druzvv-hash/r1-s3-logger/NOTES.md

# Current memory entry point

## 2026-09-28 — R3 PowerBox mechanical/interconnect baseline

FINAL PRE-ROUTING / NOT ROUTED: PowerBox now has six 3.2 mm NPTH M3 holes
with 8 mm four-layer keepouts, optional DNP J12 primary 2x8 and J13 isolated
2x5 generic 2.54 mm THT interfaces, and a dimensioned future-R3 envelope.
Exact coordinates/pinouts are in
`hardware/kicad/R3_PowerBox/docs/R3_BOARD_TO_BOARD_INTERFACE.md`. Use 15 mm
stack spacing: U3/U6 are 11.1 mm high, so 12 mm is conditional on upper-board
cutouts. Latest validation: 199 footprints including 6 PCB-only holes, 0
tracks/0 vias, ERC 0 errors/412 generator warnings, and zero clearance,
copper-edge, drill, annular, hole or courtyard DRC errors. Do not route until
the documented programming, thermal, enclosure, header/socket and bench gates
are closed.

## 2026-09-28 — R3 PowerBox KiCad workspace

FINAL PRE-ROUTING / NOT ROUTED: the canonical editable PowerBox source is
`hardware/kicad/R3_PowerBox/tools/generate_hierarchical.py`; generated KiCad,
PDF, BOM and reports are committed under the same project. The approved board
is 160 x 80 mm with 191 placed footprints, four copper layers, DIRTY -> PRIMARY
-> ISOLATION -> CLEAN zoning and a 3.0 mm all-layer functional-isolation
corridor. The architecture is 2S Li-ion -> BQ28Z610 -> BQ25798/STUSB4500 ->
switched `VSYS_MAIN` -> existing digital and isolated ADS/INA supplies.

Normal user power uses Q4 `DMP3007LSS-13`; BMS, PD and charging remain alive
when R3 is off. QON is a separate service/ship wake input. Raw BQ25798 STAT and
3.3 V `CHARGE_STATUS` are isolated by BAT54WS; J11 is the primary-only panel
interface. Latest checks: schematic PDF 11 pages, ERC 0 errors / 408 generated
library-grid warnings; critical PCB DRC geometry categories are zero; PCB has
0 tracks and 0 vias. Do not begin routing or order hardware until the blockers
in `docs/VERIFICATION.md` are closed: PD/BMS programming, Q2/Q3 and PPTC thermal
validation, TPS54302 at 6 V, RS3/INA light-load behavior, enclosure connector
clearance and approval of the functional-isolation rule.

## 2026-09-24 — shared session files and BLE resilience

R1 0.38 / CANBox 0.6.5 / R3 CC 0.2.1 deployed; STM32 CM7 LFN/UTC update
ST-LINK verified. R1/CANBox share UTC/group basenames and continue through BLE
loss; explicit offline STOP reconciles original session on reconnect. Hardware
R1/R3-controller tests PASS with no CAN frames; R1 finalized file integrity PASS.
Actual FatFs host test validates creation/modification fields and LFN. STM32
recording awaits ADS131 development (owner clarified), not yet ECO1 group member.
Earlier R1 HTTP outage cause unresolved; final short download PASS. No overnight
or load qualification. Viewer reader updated; running server needs restart.
[Contract, evidence, deployment and limits](../GLL%20CANBox/docs/SESSION_RESILIENCE_2026-09-24.md).

## 2026-09-23 — shared owner manual

Created the Ukrainian ecosystem manual with topology, entry points, workflows,
troubleshooting and evidence limits. Update it alongside user-visible changes.
Documentation only; no new build, firmware deployment or hardware acceptance.
[Manual](../lily-logger-r3/docs/manual/README.uk.md).

## 2026-09-23 — R3 primary CANBox integration verified

R3 now controls R1 and CANBox together and provides coarse UTC. R1 firmware
unchanged. Group START/STOP, saved R1 fallback and return to R3 passed;
25/25 post-return fresh/time samples, not precision acceptance. Canonical report:
../lily-logger-r3/docs/CANBOX_CONTROL.md. Existing averaging owner edits preserved.

## 2026-09-23 — CAN Live update deployed

Shared CAN assets deployed by OTA alongside existing0.37 owner changes.
88 tests/build PASS; real UI122722/0 live-ring losses, not hardware losslessness.
R1↔R3 unchanged; CANBox UTC invalid/service adapter missing.
See [deployment report](docs/CAN_LIVE_FIXES_2026-09-23.md).

## 2026-09-22 — shared CAN workspace

0.36-can-live-dev deployed via native COM9 to verified active app1 at 0x490000;
READY, generation 6. CAN tab and `/can`, preserving 0.35 OTA/timezone. Canonical
assets: ../GLL CANBox/workspace; contract: ../GLL CANBox/docs/CAN_WORKSPACE.md.
BLE service-only; browser traffic directly over CANBox USB/Wi-Fi. 88 tests/build
PASS; real R1-hosted CAN page + CANBox Wi-Fi 60 s, 12/12 concurrent BLE/time
samples PASS while idle. No loaded CAN/TX qualification. Fallback mode enabled.

## Memory checkpoint — 2026-09-21

### Current state and evidence
BENCH TESTED within the bounded 2026-09-21 report: 0.35-ota-dev deployed, browser OTA app0 -> app1; local display offset saved at +120, EEPROM generation 6. Do not assume live IP/COM/firmware remain unchanged.

### Canonical references
- [docs/R1_S3_PLAN.md](docs/R1_S3_PLAN.md)
- [docs/DEVICE_UI_AND_TASKS.md](docs/DEVICE_UI_AND_TASKS.md)
- [docs/FILE_FORMAT_V2.md](docs/FILE_FORMAT_V2.md)
- [docs/UART_DIAGNOSTICS.md](docs/UART_DIAGNOSTICS.md)
- [docs/RATE_BENCHMARK.md](docs/RATE_BENCHMARK.md)
- [docs/OTA.md](docs/OTA.md)
- [docs/R5_FEATURE_MIGRATION.md](docs/R5_FEATURE_MIGRATION.md)

### Negative knowledge / do not repeat
UART/CP210x: cleaning and cable changes did not prove a root cause; keep cause unresolved, see UART_DIAGNOSTICS. Native USB is a separate path; see CANBox stability report for core affinity evidence. Do not equate 300 Hz clean transport with analog accuracy, or a closed directory enumeration with a held SD transfer. Do not replace R5 tools with a reduced viewer and claim feature parity.

### Open work
Automatic timezone/DST and shared display-zone propagation remain IDEA; only R1 fixed local offset is deployed. Extend OTA fault/power-loss qualification, loaded UART isolation and noise/calibration qualification. Encoder remains a stub. Unified viewer work stays in lily-viewer.

### Dependencies
R3 time/control authority, CANBox fallback control, lily-viewer file readers; TTGO is an OTA/network reference only.

Shared time/control contract: [R3 ECOSYSTEM_CONTROL](../lily-logger-r3/docs/ECOSYSTEM_CONTROL.md). Read the sibling notes before changing it. A shared local timezone remains a requirement, not a completed cross-device feature.

---

# R1-S3 ideas and continuity

Read before changes and revisit at scope/milestone changes.

- [Engineering plan](docs/R1_S3_PLAN.md): acquisition, PSRAM buffering, SD block writer, UI and migration.
- [Migration history](docs/R1_MIGRATION.md): historical implementation and validation.
- [Work reports](WORK_REPORT.md): current dated work, tests, deployment and remaining tasks.
- [Ecosystem time](docs/ECOSYSTEM_TIME_SYNC.md): R3 Control Center is the preferred clock; R1 runs autonomously without it.
- R3's sibling `NOTES.md` contains ecosystem ideas and hardware evidence; review relevant entries rather than assuming all features are already implemented in R1.

## 2026-09-21 owner requirements

- Expose manual calendar entry and browser-clock fallback when valid R3 time is absent.
- Preserve authenticated Control Center priority; never move RTC during recording.
- Maintain separate project work reports; preserve existing ideas and notes.

## 2026-09-21 shared Wi-Fi

Use TTGO-style saved station networks and mDNS, keeping the R1 AP as a recovery
path. Credentials belong in private bootstrap/NVS, never notes or Git history.
Review WORK_REPORT.md for actual deployment and LAN validation.

## 2026-09-21 unified operator time

Owner requirement: every device must show the same synchronized local calendar
clock, including device screens, web panels, file lists, recording filenames and
viewer timelines. Operators must not have to mentally convert UTC. R3 Control
Center supplies the preferred clock AND the shared display timezone; standalone
manual/PC setup supplies the fallback. Do not choose each browser's timezone
independently. Keep canonical UTC/sample timing internally for cross-device
alignment and backward compatibility, and store the recording's timezone/offset
so historical display remains stable after travel or daylight-saving changes.
Existing UTC recordings must not be reinterpreted as local timestamps.
This requirement is recorded; cross-device timezone propagation is not yet
implemented. See WORK_REPORT.md.

R1-only implementation: 0.34-local-time-dev uses the existing saved offset for
UI/OLED/new filenames; PC sync refreshes that offset. Automatic DST and shared
R3 timezone distribution remain deferred. See docs/uk/TIME_SETTINGS.md.

R1 0.35 includes browser OTA (/update); see docs/OTA.md and the physical acceptance
in WORK_REPORT.md. Keep OTA idle-only and preserve storage/acquisition ownership.
