druzvv-hash/r1-s3-logger/docs/ECOSYSTEM_TIME_SYNC.md

# R3 / R1-S3 / CAN time synchronization

Architecture decision, 2026-09-09. Owner requirement: R1-S3 must connect to R3
over Bluetooth and understand its time beacon. Correlate voltage/current/energy
from R1-S3, fast sensor signals from R3, and CAN events on one timeline.
[Engineering plan](R1_S3_PLAN.md) · [S1 BLE operation and wire contract](BLE_LINK.md) ·
[Owner notes](uk/ECOSYSTEM_TIME_SYNC.md).

Requirement amendment, 2026-09-09: R3 is also the main panel for START/STOP on an
explicit selection of connected instruments. Enrolled devices must reconnect on
boot and correct their RTC from R3 when available. The
[canonical coordinator contract](https://github.com/druzvv-hash/lily-logger-r3/blob/main/docs/ECOSYSTEM_CONTROL.md)
defines E1–E5 operational delivery; [owner explanation](uk/ECOSYSTEM_CONTROL.md).
PANEL v0.24 implements saved trust, idle coarse RTC correction, selected-device
commands and static CSV v2 provenance. Host checks and a
[bounded two-board bench](ECOSYSTEM_ACCEPTANCE_2026-09-09.md) pass; remaining
physical cases are listed in that report. [Current operator guide](ECOSYSTEM_CONTROL.md). Precise alignment and
dynamic clock records remain separate S2/S3 work.

## Implementation boundary

| Part | Status |
|---|---|
| R3 RV3028 authority and `$TMB` | UART to STM32 retained; S1 BLE wraps the same coarse metronome snapshot |
| R1-S3 legacy decoder/tracker | Portable `r3_time_beacon.h/.cpp`; S1 runtime adapter feeds validated BLE observations into the tracker |
| R3 BLE server / R1-S3 BLE client | S1 implemented; short authenticated link/reconnect and 50/150/300 Hz recording/file bench passed; expanded qualification pending ([results](BLE_ACCEPTANCE_2026-09-09.md)) |
| BLE operation and diagnostics UI | v0.24 saved authenticated association, explicit time-only/remote permission, ON/OFF/FORGET and diagnostics; host-tested; bounded permission/control/recovery bench passed |
| Offset/drift model and synchronized file records | S2/S3 design below; not implemented or physically qualified |
| DS3231, sample timing, EEPROM and CSV v1 | Idle RTC correction added; sample timing and EEPROM config unchanged; v1 reader compatibility retained |
| Saved enrollment, boot reconnect and downstream RTC correction | E1/E2 implemented; saved permissions, automatic recovery and idle/deferred correction passed the bounded two-board bench; invalid source RTC/hard power-cut cases remain untested physically |
| R3 selected-device registry and group START/STOP | E3/E4 implemented for downstream BLE nodes, up to three; own STM32 recorder and CAN adapter excluded |
| Static group/RTC file provenance | CSV schema 2 implemented and cross-reader host-tested; no offset/drift model or dynamic clock-event stream |

R3's RV3028 is the owner-designated preferred RTC and sole ecosystem time
authority. This choice does not supply a measured UTC accuracy or alignment bound.

The CAN sniffer's source/board and timestamp contract have not been audited here.
Do not assume it already supports BLE or hardware bus-arrival timestamps.

## Shared timeline

For example, compare a CAN command with current rise, supply sag and sensor
response. Keep each device's native sample rate and timestamps. Alignment does
not increase R1-S3 bandwidth, eliminate INA228 sequential-channel timing or prove
causation. A shared test/group ID associates independently started recordings;
equal filenames and START reception times cannot align their samples.

```mermaid
flowchart LR
  RTC[RV3028 UTC] --> CC[R3 Control Center: time authority]
  CC -->|existing UART TMB| ADS[R3 STM32: DRDY clock]
  CC -->|S1 BLE coarse observations| R1[R1-S3: monotonic clock]
  CC -.->|adapter to qualify| CAN[CAN: capture clock]
  ADS --> RF[R3 data + clock evidence]
  R1 --> LF[R1-S3 data + clock evidence]
  CAN --> CF[CAN data + clock evidence]
  RF --> VIEW[Viewer: shared timeline and uncertainty]
  LF --> VIEW
  CF --> VIEW
```

## Existing R3 protocol and limitations

Read-only audit of `lily-logger-r3`, HEAD `cdfa3b9` with local modifications.
References describe the inspected working tree, not a newly tested release.

| Source | Finding |
|---|---|
| `cc/src/main.cpp:2298` | `send_time_metronome_beacon()` writes the line below and flushes UART |
| `cc/src/main.cpp:12119` | CCTX UART1, TX15/RX16, 2,000,000 baud, 8N1 |
| `cc/src/cctx_time.cpp:519` | Software poll about once per second; sequence increments, skipping zero on wrap |
| `cc/src/cctx_time.cpp:640` | Integer RTC seconds read twice, separated by 2 ms |
| `cc/include/cctx_time.h:7` | RV3028 INT unused; no captured RTC second edge |
| `firmware/stm32/CM4/Core/Src/mbx_cm4.c:235` | CM4 also accepts historical/ambiguous alternate field orders |
| `firmware/stm32/CM7/Core/Src/sd_filelog.c:1535` | TCHK extrapolates later RTC/metro values from elapsed local time and the starting anchor |

```text
$TMB,<seq>,<unix_s>,<valid>,<last_tick_ms>\n
```

Unsigned decimal u32 fields, except `valid` exactly 0/1. Sequence runs 1 through
UINT32_MAX then 1. `last_tick_ms` is R3 ESP `millis()` captured before the RTC poll;
it wraps and is not the receiver's uptime. `valid=0` is valid packet evidence,
but not valid UTC. A sequence gap measures missing generated beacons, not seconds.

The new R1-S3 decoder accepts the exact current emitter layout, canonical decimal
and LF, maximum 40 bytes. It rejects overflow, truncation, extra fields, CR/NUL and
alternate-order guessing. The tracker preserves raw decoded/accepted observations,
u64 local receive time and explicit connection segments. It counts malformed,
duplicate, reordered and missing packets, and handles R3's zero-skipping wrap.
Freshness expires at 5 seconds; decoded invalid-time evidence revokes UTC
eligibility. Eligibility means only fresh sender-valid evidence, never clock lock.
It has no allocation, radio dependency, RTC write or UTC offset calculation.
Use a single owner; the tracker is not a stream framer or cross-core queue.

Legacy TMB lacks version, device/boot ID, clock revision, uncertainty, transmit
capture, CRC and authentication. A restart without reconnect cannot be reliably
distinguished from old packets. UART/BLE adapters must bound and frame complete
messages; never pass partial notifications as complete beacons.

The RTC validity flag does not establish accuracy against UTC. Integer-second
software polling does not prove millisecond phase accuracy. R3 DATA/DTBM preserve
the local ADC clock; existing TCHK/TCKS are not repeated precise captures of real
received beacons. A measured bridge from CC monotonic time to STM32 DRDY time is
still needed. The current implementation establishes no inter-device error bound.
The audited R3 documents reserved BLE for future service links and proposed
RS-485 for precise sync; S1 now implements the coarse BLE service.

## S1 BLE contract and remaining clock exchange

Use **Bluetooth LE GATT**: R3 peripheral/server, R1-S3 central/client selecting
one R3. ESP32-S3 supports LE rather than Classic SPP; see the
[Espressif stack overview](https://docs.espressif.com/projects/esp-idf/en/stable/esp32s3/api-guides/ble/overview.html).
R3 should support R1-S3 and a capable CAN node together; other CAN hardware needs
a qualified gateway/wired adapter.

S1 now shares an identical `r3_ble_protocol.h` in both repositories, with stable
project UUIDs, exact byte lengths, little-endian fields, identity/boot/revision,
coarse-only capability and CRC32. Protected identity reads are 36 bytes; complete
beacon notifications are 64 bytes, requiring ATT MTU at least 67 (preferred 128).
Full offsets and operation are documented in [BLE_LINK.md](BLE_LINK.md). The
current ECO1 request/control extension uses 96-byte frames and requires MTU 99;
the S1 36/64-byte layouts remain unchanged.
Short physical bench results are available; expanded radio and clock qualification
remain pending. The richer synchronization interface still
needs the following work:

- **Identity/capabilities (read):** extend the implemented device/boot/role/version
  and transport limits with a time-domain ID and qualified exchange capabilities.
- **Beacon (notify):** S1 carries sequence, boot/revision, CC software capture,
  legacy integer RTC seconds/tick, UTC validity and explicitly unknown uncertainty.
  It is a coarse snapshot, not an RTC edge or a qualified precise anchor.
- **Exchange (request/reply):** request ID, local send t1, R3 receive t2 and reply
  send t3; R1 captures t4 immediately on notification entry. Match IDs/boot/revision
  and reject expired replies. Define each capture point and timestamp resolution.

S1 rejects smaller MTUs instead of fragmenting notifications, detects sequence
gaps and validates identity/version. Discovery, subscription and capped backoff
run on a separate core-0 worker. Future exchanges must define bounded framing,
request IDs, lengths and expiry rather than assume one notification always fits.
Select R3 explicitly in UI. Current v0.24 uses passkey-authenticated LE Secure
Connections, disables legacy pairing and enables persistent authenticated bonds.
Each new link authenticates, validates identity and subscribes again. Keep keys
and pairing output outside public profiles/logs.

The earlier S1 selection was volatile. E1 now replaces it with explicit Save
of a versioned association/permission policy and NVS bonds on both sides.
SAVE 0 permits time only; SAVE 1 explicitly permits remote recording. Boot
reconnect and bounded retries use saved trust, never a saved/replayed PIN.
Unenrolled or incompatible policies do not authorize a random nearby R3.
ON resumes saved retries; OFF is temporary; FORGET removes association/bond.
Connection does not automatically start logging. Existing measurement settings
and EEPROM config-v1 are preserved; no per-beacon EEPROM writes occur.

## Clock model and failure behavior

Keep three concepts separate: immutable local acquisition time; common R3
monotonic time; optional UTC anchor. Relative correlation can work without UTC.
Represent mappings in segments around nearby integer origins:

```text
r3_us = r3_origin_us + scale * (local_us - local_origin_us)
utc_us = utc_origin_us + (r3_us - utc_anchor_r3_us)  [valid anchor only]
```

Retain raw observations as well as fitted offset/drift and model version. Stored
stamps are integer microseconds; frontend JSON represents u64 values as decimal
strings. Never adjust sample timestamps, acquisition deadlines or integration dt.

At approximately equal rates, an initial four-stamp R3-minus-local offset is
`((t2-t1)+(t3-t4))/2`; residual RTT is `(t4-t1)-(t3-t2)`. Repeated low-delay
exchanges estimate offset/drift. Asymmetric radio/host delay remains uncertainty.
Reject negative/excessive RTT, mismatched replies and discontinuities; account for
capture resolution, queue delay and source accuracy. Never assign `unix_s*1e6`
to the receiver callback or use a nominal BLE interval as a guaranteed error bound.

| State | Meaning |
|---|---|
| Disabled / searching | Autonomous recording; no current shared-clock claim |
| Connected, unqualified | Transport alive; insufficient timing evidence; legacy TMB provides coarse association only |
| Locked | Versioned model passes explicit residual/age/error-budget gates |
| Holdover | Link lost; previous model ages with increasing uncertainty from qualified drift bounds |
| Expired / invalid | Error bound unknown or age limit exceeded; local recording continues |

Five-second legacy freshness is not a lock criterion. Without qualified drift
bounds, holdover uncertainty becomes unknown immediately. Report UTC validity
separately from relative-clock quality. Peer reboot, source/clock revision change,
time jump or ambiguous reset begins a new segment; do not join them silently.
Automatic master election is outside the initial scope.

DS3231 remains the offline wall clock. E2 corrects it from fresh valid time
of the enrolled R3 at startup/first available link through the existing I2C owner
while idle. Defer during STARTING/RUNNING/STOPPING and file closure, then request
fresh evidence and revalidate its age, source boot and revision before applying.
Reconnection/revision changes trigger revalidation, not unconditional writes.
Never propagate invalid R3 time or write RTC/EEPROM on every beacon. Verify RTC
readback and distinguish calendar correction from qualified S2 clock lock.
Losing BLE neither stops a session nor rewrites past UTC. New CSV v2 files keep
their frozen starting anchor and static correction evidence; dynamic clock
events remain future work.

E2 limits source RTC read age to 1,500 ms, request roundtrip to 1,000,000 us and
receive-to-application delay to 1,000,000 us. These are freshness gates, not a
qualified accuracy bound. [CSV v2](FILE_FORMAT_V2.md) explicitly supports a known
UTC anchor with unknown uncertainty (null); both readers enforce the correction
evidence contract. Its writer uses unknown uncertainty, avoiding the historical
CSV v1 1,100,000 us claim for an unqualified R3 path. V1 fixtures/readers remain
unchanged. RTC correction and deferral passed the
[bounded bench](ECOSYSTEM_ACCEPTANCE_2026-09-09.md); its freshness gates do not
establish precise accuracy, and invalid source RTC was not exercised physically.

## Ownership and buffering

Core 0 owns S1 BLE discovery/client lifecycle alongside UI; clock estimation is
future work.
Callbacks only capture local time and copy bounded data; no I2C, SD, EEPROM, JSON
or blocking operations. Core 1 retains acquisition/I2C at highest application
priority plus the separate lower-priority sole SD owner. Pass bounded messages
and snapshots; do not expose mutable clock/config state across tasks.

Preserve PSRAM sample FIFO and 8 KiB internal output staging. S1 uses an eight-entry
R3 observation queue and a 12-entry R1 notification queue, with counted overflow.
The separate persistent clock-event path remains planned (initial target: 64
fixed-size entries); avoid per-packet allocation. The SD owner orders/associates
persisted evidence by local capture time, not
callback scheduling. Sync overflow is counted and invalidates sync coverage;
it must not discard samples or block the producer. Persist relevant evidence before
claiming file synchronization; RAM-only status is insufficient.

BLE and Wi-Fi share the radio; core affinity does not remove contention. Qualify a
pinned Arduino-compatible BLE stack with the current AP UI and toolchain before
enabling it by default. Measure internal heap/stack, queue drops, RTT/residuals,
sample lateness and SD latency. See [Espressif RF coexistence](https://docs.espressif.com/projects/esp-idf/en/v5.1/esp32s3/api-guides/coexist.html).

## Files and viewer

Native schema 1 remains unchanged. [Schema 2](FILE_FORMAT_V2.md) now carries
static device/boot/recording/group/coordinator identities and nullable coarse
RTC correction evidence, repeated in every rotated part and accepted by both
readers. It does not implement the full precise synchronization event model.
That future extension requires an explicit compatible version/reader contract,
not extra v1 columns or unrecognized comments. It must carry:

- device/local boot ID, shared test/group ID and independent recording ID;
- authority device/boot/domain/clock revision and mapping segment;
- local/remote captures, optional UTC anchor, offset/drift, uncertainty and validity interval;
- original beacons/exchanges, capture method, model version and quality;
- loss, reconnect, step, holdover/expiry and overflow events protected by file
  integrity, with rotation linkage and interrupted-file recovery.

Each rotation part needs the current model and its qualifying evidence for
self-contained interpretation. Only the SD owner writes these records. Energy
continues using local elapsed time. Legacy export warns when sync evidence is lost.

Viewer adapters preserve R1, R1-S3 v1, R3 and CAN originals. Shared time is an overlay
with uncertainty per segment, not destructive resampling. If error intervals overlap,
event order is unresolved. Unknown historical relationships stay unknown; manual
marker alignment is a labelled user estimate. Existing v1 readers must keep passing.

## Delivery order and gates

The owner now prioritizes E1 trust/reboot reconnect, E2 startup RTC, E3 targeted
session-safe control, E4 R3 selection UI and E5 versioned group/time evidence.
Use the coordinator contract for those gates. E1–E4 and the static provenance
subset of E5 are implemented in v0.24 and host-tested; a bounded two-board
permission/RTC/control/recovery bench passed with verified files. See the
[remaining physical gates](ECOSYSTEM_ACCEPTANCE_2026-09-09.md). S2 remains the
separate precision investigation. S3 must extend
the explicit schema 2 contract compatibly. S1 transport acceptance alone does
not qualify the new enrollment, RTC or control behavior.

| Stage | Deliverable | Acceptance |
|---|---|---|
| S0, completed foundation | Audit, legacy decoder/tracker, architecture | Host malformed/wrap/stale tests and normal build; no radio claim |
| S1, short bench passed; expanded qualification pending | Shared BLE contract, R3 server, R1 client, volatile peer/PIN selection and diagnostics | Correct/wrong PIN, reconnect and three verified SD files passed; remaining radio edge cases/endurance and 300 Hz signal-quality investigation are open |
| S2 | Offset/drift/error model, CC-to-DRDY bridge, CAN clock audit | Shared physical event and independent reference establish error bounds |
| S3 | Versioned files/readers, owner queues, UI quality and saved policy | Golden/corruption/rotation/reboot tests, backward compatibility and autonomous operation |
| S4 | R1-S3 + R3 + actual CAN node | End-to-end alignment and endurance; no silent time jumps or optimistic lock |

S1 changes both repositories while retaining R3 UART behavior and local work.
Its targeted physical bench passed; complete the remaining radio/clock gates
before broad acceptance. The file/transport result does not qualify the observed
300 Hz current spread.
Keep synchronization work separate from the unresolved UART endurance fault.
The historical S0 validation below did not flash firmware or test physical BLE.

Bench matrix: R1 at 1/50/300 Hz, representative R3 high-rate recording, Wi-Fi UI
active/absent, allowed download load, multiple BLE clients, poor reception,
disconnect/reboot of each node, RTC invalid/step, long holdover and full event queue.
Compare a shared electrical event within all channel ratings using an independent
timing reference. Publish p50/p95/max residuals, uncertainty, duration and failures.
If measured BLE precision is insufficient, qualify a wired edge/SYNC-Link. Do not
promise millisecond accuracy or infer it from formatted microsecond timestamps.

## Source fingerprints

S0 validation, 2026-09-09: `python -m unittest tests.test_r3_time_beacon
tests.test_sample_clock tests.test_recording_format tests.test_contracts -v`
passed all 24 tests, including both production/reference CSV paths. The new
portable core compiles with `-Wall -Wextra -Werror`. `pio run -e esp32-s3`
passed; no upload performed. Independent review checked the decoder and sequence
arithmetic against the actual R3 emitter.

SHA-256 of the inspected R3 working-tree inputs:

```text
cc/src/main.cpp
e405c316e2f89f8f9ed36d129fd7613fa9419df32297d1dce391647d6d687a15
cc/src/cctx_time.cpp
0eeed7dc5f03ad81fcd03aedffcf94120cf71415f121794ab6f477ee80cd47ae
firmware/stm32/CM7/Core/Src/sd_filelog.c
fe513abf1c67132159c37b42de05c69d161bc1bf9c750d7c4f0a47de7486f751
```
