druzvv-hash/r1-s3-logger/docs/SD_DOWNLOADS.md

# SD file browser and download (PANEL v0.21)

The device panel now lists directories and downloads existing files from microSD.
File browsing/download reads the card; the [P5 recorder](P5_RECORDING.md) writes
sessions separately. Existing hardware-test files can also be retrieved without
removing the card.

## User flow

Open **Файли SD** to read the current folder automatically. The compact table has
its own scroll area, sticky headers, local start dates and sizes. Use breadcrumbs,
the parent button or **Записи** to navigate. Select a file and choose **Завантажити**,
use its download icon, or double-click the name. Arrow keys move between names;
Enter opens a folder or downloads a file.

Search and sorting cover every loaded entry in the current folder. Type filters
offer CSV and unfinished PART files while keeping folders visible. The browser
automatically requests all six-entry device pages; a partial-list notice stays
visible until enumeration completes. **Зупинити** cancels enumeration and releases
its directory cursor. Navigation, download and START wait for that cursor to close.
On narrow screens the table scrolls horizontally inside its own viewport.
The browser download manager displays progress, cancellation and the final result.
No deletion, formatting or card uploads are exposed.

USB uses the existing loopback bridge. Wi-Fi uses the ESP AP panel; its download
route redirects to a dedicated server on port 81 so a long transfer does not occupy
the main panel server on port 80. UART and HTTP remain on core 0. A lower-priority
SD task on core 1 owns runtime mount/read/close operations, separate from acquisition
and the I2C owner. Runtime SD diagnostics also use this owner.

## Transfer contract

- `GET /api/files?command=LIST%20<path-hex>` opens a directory and returns the first
  page; `NEXT <session>` continues it. Entries contain literal name, directory flag,
  byte size and hexadecimal UTF-8 absolute SD path.
- `OPEN <path-hex>` returns a random nonzero session ID, size and 2048-byte block limit.
- `READ <session> <offset>` returns session, size, offset, data hex and IEEE CRC32.
- `CLOSE <session>` releases the card. Completed directory enumeration closes itself.
- `GET /api/download?path=<path-hex>` streams an attachment with its original name and
  exact Content-Length. USB endpoints additionally require the current session token.
- UART carries these commands as `PANEL <request-id> FILES <command>`; its existing
  request lock is released between chunks so state/live polling can interleave.

USB verifies every chunk's session, offset, size, exact byte count and CRC before
sending it to the browser. A mid-transfer error closes the HTTP connection before
Content-Length is satisfied, leaving a failed/incomplete download. There is no
automatic retry that could mix different files or boots. Restart an interrupted
download from the beginning. Native Wi-Fi streams the same bounded SD reads using
TCP transport integrity. Neither ESP nor bridge buffers the whole file.

One file/directory session is active at a time. Concurrent opens and SD rechecks
receive a busy response. Idle sessions expire after 30 seconds; downloading a file
closes that browser's directory cursor. Refresh the directory to enumerate again.
Paths reject traversal, control characters, backslashes and drive prefixes; paths
longer than 239 bytes appear disabled. Filenames are rendered as text in the UI.

## Integration boundary

The [v0.18 recorder](P5_RECORDING.md) uses the same SD owner and excludes all file
requests before it starts writing. START is refused while a transfer is open;
downloads require READY or ERROR after storage has closed. There is no active-file
snapshot. Sampling continues while downloading, but UART bandwidth limits live delivery and USB transfer
speed; a 1 GiB file will take a long time at 115200 baud with hex framing.

## Validation

Host tests cover binary and empty downloads, Unicode attachment names, traversal and
command rejection, wrong session/offset/size, bad CRC, short chunks and disconnects.
Browser acceptance covers listing, literal filenames, folders, downloading bytes and
mobile layout. The 601-entry fixture additionally covers complete-directory search,
sorting, scrolling, cancellation and literal hostile-looking filenames. Hardware
results are recorded in R1_MIGRATION.md after deployment.
