druzvv-hash/r1-s3-logger/docs/uk/BLE_LINK.md

# Зв’язок R3 ↔ R1-S3 через BLE

PANEL v0.24, 09.09.2026. Тести на ПК та
[обмежений тест двох плат](../ECOSYSTEM_ACCEPTANCE_2026-09-09.md) пройдено:
збережені дозволи, RTC, віддалене керування й відновлення після перезапусків.
Розширені апаратні перевірки залишаються відкритими.
[Повна інструкція](ECOSYSTEM_CONTROL.md) · [Транспорт англійською](../BLE_LINK.md).
[Короткий тест S1](BLE_ACCEPTANCE_2026-09-09.md) описує попередню версію.

## Перше підключення

1. Зупини запис R1. У USB-консолі R3 виконай `ble pair`: на 120 секунд
   відкриється додавання приладу й з’явиться тимчасовий PIN. Якщо BLE вимкнений,
   спочатку `ble on`; `ble?` показує стан без PIN.
2. На R1 відкрий **BLE · R3**, знайди та вибери адресу свого R3, введи PIN
   і натисни **Підключити**. Поле PIN очиститься після надсилання.
3. Після підтвердженого з’єднання явно збережи прив’язку. Без дозволу
   віддаленого запису — лише час (`SAVE 0`); із дозволом — час і керування
   (`SAVE 1`). Це не кнопка збереження вимірювальних налаштувань EEPROM.

Після Save R1 сам знаходить свій R3 при ввімкненні й відновлює зв’язок після
обриву. Паузи повторів — 1, 2, 4, далі до 8 секунд. Кожне підключення
перевіряє довіру, ідентичність і підписку заново; збережений PIN не потрібен.
BLE-хост зберігає ключі захищеної пари в NVS, а не у файлах чи EEPROM.

**OFF** вимикає BLE до наступного ввімкнення або **ON**. **ON** відновлює
збережений зв’язок. **FORGET** видаляє прив’язку й ключі на R1; після цього
потрібне нове явне додавання. При видаленні довіри чи заміні плати прибери
старий запис також на R3. Назва знайденого приладу сама по собі не є доказом довіри.

## Що показує панель

- **Збережена прив’язка** та **дозвіл керування** — два окремі параметри.
- **Захищене з’єднання** — підтверджений BLE-зв’язок із вибраним R3.
- **Свіжий маяк** — коректний новий пакет, якому менше п’яти секунд.
- **RTC звірено з R3** — власник I²C виконав грубу календарну корекцію для
  цього запуску та ревізії часу R3. Під час запису корекція чекає.
- **Діагностика** — вік/номер маяка, пропуски, помилки, повторні підключення,
  запуск R3, ревізія часу і MTU. Втрата BLE не зупиняє запис.

Поточний профіль ECO1 вимагає MTU щонайменше 99, запитує 128. Старі маяки S1
залишилися 64-байтовими; розширення керування має 96 байтів. Захист —
LE Secure Connections із підтвердженням PIN під час додавання та постійними
ключами пари. Старий метод pairing вимкнений.

Точність вирівнювання відліків поки невідома: `synchronized=false`,
`coarse=true`, `uncertainty_us=null`. Частота вимірів, монотонний час,
інтегрування енергії та FIFO у PSRAM не прив’язуються до приходу маяка.
CSV v2 зберігає походження групи та RTC, але не точну модель синхронізації.
Ключі, PIN і токени доступу до панелі не додаємо до публічних нотаток.
