druzvv-hash/r1-s3-logger/docs/uk/UART_DIAGNOSTICS.md

# Перевірка UART після заміни кабелю — 2026-09-08

Збій повторився і з новим кабелем. Десять відкриттів COM5 пройшли нормально,
але перший автоматичний вхід у завантажувач завершився помилкою. Прошивку
під час цієї перевірки не перезаписували.

Після цього UART не відповідав, а стартові повідомлення приходили частково
пошкодженими. Водночас через Wi-Fi логер працював: усі 12 перевірок показали
нові виміри. Отже, цього разу весь ESP32 не завис.

Через Wi-Fi повернуто початкові 100 Гц. EEPROM не змінювали. Програмний
перезапуск CP210x Windows відхилив через брак прав; потрібне фізичне
відключення й повторне підключення USB. Після нього спочатку перевіряємо
тривалу передачу UART, потім повторюємо автоматичний вхід у завантажувач.

Причина ще не встановлена: новий кабель не усунув проблему повністю, але
порівняння зі старим кабелем в однакових умовах ще не було. Тривалий тест
UART не пройдено — його не вдалося розпочати через втрату зв'язку.

[Технічний звіт і результати](../UART_DIAGNOSTICS.md).

## Повторна перевірка з журналами ПК і стану логера

Після наступного перепідключення збій був уже до нового Reset. Зберегли сирі
байти UART на ПК і паралельні знімки стану логера через Wi-Fi. Додаткові
лічильники всередині UART-драйвера ESP32 не встановлювали.

У контрольному сеансі правильними були 143 із 156 відповідей. Windows сім
разів повідомив **CE_FRAME (0x0008)** — помилку UART-кадру на прийманні.
Повідомлень про переповнення буфера не було. Пошкодження виникали і при
читанні рядками, і при читанні блоками.

Водночас 55 Wi-Fi-знімків мали той самий ідентифікатор запуску ESP32, а
лічильник вимірів виріс на 1882. Це не повне зависання логера. Підключення
до його Wi-Fi не гарантує справного UART: повторний сеанс теж дав помилки.

Наступний вимір — сигнал на **TX ESP32 (GPIO43)** та на вході **RX CP210x**,
разом із перевіркою живлення й загальної землі. Зараз найкраще підтверджена
проблема на рівні приймання UART; конкретну мікросхему чи контакт ще не
визначено. Прошивку під час цих тестів не міняли.

## Після ще одного промивання спиртом

ЛБЖ вимкнений, дроти залишилися підключеними — підтверджено власником.
На час тесту встановлено 300 Гц без збереження в EEPROM.

- За 471,5 секунди пройшло 1578 запитів без помилок.
- Через UART завантажено наявний файл 1,74 МБ: CRC32 кожного блока та SHA-256
  цілого файла збігаються. Новий запис навантаження не створювали.
- Під час передачі не було помилок UART-кадру, пропущених/некоректних вимірів
  або несподіваного перезапуску.
- Десять повторних відкриттів порту пройшли успішно.
- Із десяти сеансів читання через ROM-завантажувач пройшло дев'ять. Перший
  увійшов у DOWNLOAD, але відповідь читання регістра обірвалася. Автоматичний
  Reset відновив роботу; наступні дев'ять спроб пройшли. Усі десять завершилися
  поверненням до READY, без запису прошивки.

Безперервний обмін зараз працює краще, але збій ROM-передачі ще залишився.
Попередні проблемні тести були з увімкненим ЛБЖ, тому результат поки не можна
приписати лише промиванню. Наступне порівняння — з попереднім навантаженням
на цій самій платі та кабелі.

Повернуто точні початкові налаштування: READY, 50 Гц, EEPROM покоління 3.
Прошивку та збережені налаштування не змінювали.
