druzvv-hash/r1-s3-logger/docs/uk/README.md

# Українські нотатки власника

[Український README](../../README.uk.md) · [English README](../../README.md)

Ці нотатки збережені для продовження роботи українською. Вони входять до відкритого репозиторію, тому не міститимуть паролів чи інших секретів.

- [Історія bring-up](bring-up-history.md) — послідовні записи тестів; старі «очікується» описують тодішній стан.
- [Спільний час R1-S3, R3 та CAN](ECOSYSTEM_TIME_SYNC.md) — ролі приладів, BLE, часові дані у файлах і порядок реалізації.
- [R3 як головна панель](ECOSYSTEM_CONTROL.md) — інструкція v0.24: збережена прив’язка, окремий дозвіл керування, час після ввімкнення та START/STOP вибраних приладів.
- [Підключення R3 через BLE](BLE_LINK.md) — пошук, PIN, повторне підключення й показники маяка; [короткий тест пройдено](BLE_ACCEPTANCE_2026-09-09.md), розширена перевірка й розкид струму на 300 Гц ще відкриті.
- [Огляд попередніх проєктів](project-context-review.md) — історична карта робочих папок та висновки.
- [Поточні результати англійською](../bring-up.md) — актуальний зведений стан.

Робоча папка тепер `C:\Projects\r1-s3-logger`, поруч із Lily R3. Старі згадки `C:\Projekts` у записах залишено як історію.

Поточний етап: PANEL v0.24 має [панель тестів](TEST_PANEL.md), запис на SD,
збережену прив’язку до R3, звіряння RTC у спокої та групове керування. Код і
тести на ПК готові; [обмежений тест двох плат пройдено](../ECOSYSTEM_ACCEPTANCE_2026-09-09.md).
Розширені апаратні випадки ще потребують перевірки. CSV v2
зберігає статичне походження групи й RTC; точне вирівнювання та CAN ще попереду.
Ранні записи про діагностику завантаження залишені як історія.

- [Знайдені вихідники R1 і в’ювер](legacy-r1-analysis.md) — огляд Logger_Analysis від 2026-09-07.
