druzvv-hash/r1-s3-logger/docs/LINKED_RECORDING.uk.md

## Оновлення 24.09.2026 — має пріоритет над історичним описом

R1 0.38 продовжує активний запис після втрати BLE/CANBox. STOP без зв’язку
закриває R1 й чекає підтвердженого завершення своєї сесії CANBox.
[Поточна інструкція](../../lily-logger-r3/docs/manual/OPERATIONS.uk.md)
і [докази та обмеження](../../GLL%20CANBox/docs/SESSION_RESILIENCE_2026-09-24.md).

# Спільний запис R1 і CANBox

Прошивка R1 0.31-canbox-dev. CANBox працює з чинним ECO1, зміна його прошивки не потрібна.

## Керування

Біля старту CANBox є перемикач **Спільно з R1**. Коли він увімкнений, кожна з двох кнопок старту запускає обидва записи, а кожна кнопка зупинки завершує обидва. Вимкнений перемикач залишає незалежне керування. UI використовує назви CANBox і CAN-логер.

Перед спільним стартом обидва пристрої мають бути вільні, CANBox — підключений, авторизований і синхронізований. Чернетку налаштувань потрібно застосувати або скинути. Приєднати вже запущений незалежний запис до спільної сесії не можна. Перемикач блокується на час запису. Після перезавантаження сторінки активний спільний запис визначається за станом R1; робота не залежить від браузера. Поза активним записом вибір перемикача діє до закриття сторінки.

## Семантика синхронізації

Це спільні Старт/Стоп, ідентифікатор групи та календарна шкала UTC. **Строго одночасного апаратного запуску немає.** R1 спочатку запускає CANBox, чекає підтвердження запису саме потрібної сесії, потім запускає власний запис. Початок CAN-захоплення передує вимірюванням R1. Точність календарного часу залишається непідтвердженою; RTC має секундну роздільність.

64-бітний ідентифікатор групи зберігається без втрати точності: `ecosystem.group_id` у метаданих R1 та `group` у CANBox `.eco`. Окремі ідентифікатори записів залишаються різними. Для групи координатором у метаданих R1 вказано цей R1 і його поточне завантаження.

Під час спільного запису R1 резервує коротку паузу читання RTC приблизно кожні 5 секунд на межі конверсії. Наступний відлік має прапорець GAP; інтегратор не заповнює цю паузу вигаданими вимірами. Це важливо для режимів, де вільного часу на I²C недостатньо: джерело часу CANBox не стає застарілим. Незалежний запис R1 зберігає попередню політику читання RTC у вільному інтервалі.

## Відмови та зупинка

Команди панелі `LINK START` і `LINK STOP` виконуються власником вимірювань R1. BLE-операції проходять через єдину чергу радіопотоку. Очікування старту CANBox обмежене 20 секундами, запуску R1 — 30 секундами від початку операції. Команди CANBox перевіряють завантаження, сесію, групу та термін дії.

Якщо одна сторона не стартувала або зникло підтвердження спільного запису, координатор зупиняє R1, потім власну сесію CANBox. Повторні STOP обмежені інтервалом у 2 секунди. Чужу сесію CANBox він не зупиняє. При втраті зв’язку стан залишається невизначеним до свіжого підтвердження; таймер не перетворює невідомий результат на успішну зупинку. Після скасування раннього старту координатор також чекає завершення строку дії вже поставленої в чергу команди.

Перезавантаження самого R1 перериває роботу координатора; відновлення керування попередньою сесією CANBox після зміни завантаження не реалізоване. Команда STOP через USB CANBox залишається способом завершити такий запис. Панель не повинна трактувати втрату R1 як зупинку CANBox.

## Перевірка

87 host-перевірок, збірка esp32-s3-usb та браузерні перевірки пройшли. Окремий тест координатора перевіряє повторний старт, запізнілий START після скасування, частковий запуск, відмову R1, втрату зв’язку, чужу сесію і повторні STOP.

Фізичний тест через COM9/COM11 підтвердив спільний запис і зупинку обох пристроїв. У контрольному інтервалі понад 32 секунди обидва записували, час CANBox залишався синхронізованим, нових обривів, помилок читання BLE та невалідних відповідей часу не було. Перед цим окремо спрацював захист від помилки SD CANBox: R1 не почав запис. Після повторного монтування картки перезапуском CANBox спільний старт пройшов.

Агреговані результати: [linked-recording-2026-09-15.json](evidence/linked-recording-2026-09-15.json). Сирі записи залишаються поза Git.

Перевірка файлів: R1 — 5098 рядків, CRC/SHA і читання у Viewer пройдено, 0 невалідних рядків, 0 пропущених номерів відліків; 10 позначених пауз RTC, фактично 99,765 Гц при заданих 100 Гц. CANBox — 64 байти, 0 CAN-кадрів, коректний END і CRC. Група у метаданих CSV R1 збігається з підтвердженою групою сесії CANBox. Файл `.eco` окремо через USB не зчитувався.
