druzvv-hash/r1-s3-logger/docs/uk/TIME_SETTINGS.md

# Місцевий час R1-S3

Починаючи з 0.34 панель, OLED і назви нових записів використовують
збережений у R1 часовий зсув. Браузер на іншому телефоні показує той самий час.

«Взяти час телефона / ПК» встановлює поточний час і, якщо потрібно, застосовує
та зберігає поточний часовий зсув ПК в EEPROM. Спочатку завершіть запис і
застосуйте або скиньте чернетку налаштувань. Ручне введення — у місцевому часі R1.
Пріоритет часу R3 зберігається; ручне встановлення недоступне за чинного часу R3.

Зсув також можна змінити в налаштуваннях і зберегти. Зараз він фіксований:
літній/зимовий перехід треба оновити кнопкою часу ПК. Для Праги влітку це
120 хвилин, взимку 60. Автоматичні правила та передача поясу від R3 — наступний етап.

Нова назва містить місцеву дату, час і зсув, наприклад
`r1s3_2026-09-21_17-39-24_+0200_...csv`. Каталог показує час, зафіксований у назві,
навіть після зміни налаштування R1. Старі UTC-назви розпізнаються й показуються
за поточним зсувом R1; самі старі файли не перейменовуються.

RTC, BLE і колонка UTC в CSV залишаються абсолютною часовою основою.
Знімок конфігурації CSV містить `display_utc_offset_min`, щоб вювер згодом міг
показувати місцевий час запису. Вювер та інші прилади в цій зміні не оновлювалися.
