druzvv-hash/r1-s3-logger/docs/uk/ECOSYSTEM_CONTROL.md

# R3: спільний час і керування приладами

PANEL v0.24, 09.09.2026. Збережену прив’язку, повторне підключення, звіряння RTC,
керування вибраними приладами та дані походження CSV v2 реалізовано в коді й
перевірено тестами на ПК. **[Обмежений тест двох плат пройдено](../ECOSYSTEM_ACCEPTANCE_2026-09-09.md):**
збережені дозволи, звіряння RTC, керування й відновлення після перезапусків.
[Попередній тест S1](BLE_ACCEPTANCE_2026-09-09.md) підтверджує попередній BLE,
але не нову збережену прив’язку чи групові команди.
[Основна інструкція англійською](../ECOSYSTEM_CONTROL.md) ·
[Точність спільного часу](ECOSYSTEM_TIME_SYNC.md).

## Один раз додати свій R3

1. Зупини запис R1-S3 і дочекайся закриття файлу. У USB-консолі R3 виконай
   `ble?`; якщо вимкнено — `ble on`. Команда `ble pair` відкриває додавання
   на 120 секунд і показує тимчасовий PIN із шести цифр.
2. У R1-S3 відкрий **BLE · R3**, знайди та вибери свій R3, введи PIN і
   підключися. Дочекайся підтвердженого захищеного з’єднання.
3. Явно збережи прив’язку. Для **лише часу** залиш дозвіл керування записом
   вимкненим. Щоб R3 міг запускати й зупиняти R1, увімкни цей дозвіл перед
   збереженням. Саме підключення ще не означає збереження довіри на наступний запуск.
4. Перевір стан збереженої прив’язки та дозволу. Після наступного ввімкнення
   логер сам підключатиметься до цього R3, навіть якщо R3 з’явиться пізніше.

| Дія BLE | Що робить |
|---|---|
| `SAVE` / `SAVE 0` | Зберігає прив’язку лише для часу. |
| `SAVE 1` | Зберігає прив’язку з дозволом віддаленого START/STOP. |
| `ON` | Відновлює підключення до збереженого R3 без PIN. |
| `OFF` | Тимчасово вимикає зв’язок і повторні спроби; після перезапуску збережена прив’язка знову діє. |
| `FORGET` | Видаляє прив’язку та ключі пари на R1. Додавання потрібно повторити. |

Панель формує ці команди сама. Дії з прив’язкою доступні між записами.
Це окреме збереження від кнопки налаштувань EEPROM. Ключі захищеного зв’язку
й версійована прив’язка живуть у NVS; PIN не зберігається. Якщо довіру стерли
або замінили плату, прибери старий запис і на R3, після чого додай пару заново.
Автоматичне підключення **не запускає запис**.

## Коли звіряється час

R3 з RV3028 — головне джерело за нашим вибором. DS3231 у R1 залишається
автономним годинником. Після підтвердженого зв’язку R1 отримує свіжий чинний
час R3, записує його через наявного власника I²C та перевіряє читанням.
Під час запуску запису, записування і закриття файлу корекція чекає; після
цього запитується новий час. Недостовірний час R3 не переноситься.

Після зміни запуску R3 або ревізії його часу потрібне нове підтвердження.
Ручне встановлення часу скидає ознаку звіряння з R3. RTC й EEPROM не
переписуються від кожного маяка. Виміри, часові мітки відліків та інтегрування
енергії продовжують використовувати місцевий монотонний час ESP.

**«RTC звірено з R3» — це календарний час із невизначеною похибкою.**
Це ще не точне вирівнювання відліків чи доказ мілісекундної синхронізації.
Чинний RTC і свіже BLE-з’єднання показуються окремо.

## Головна панель R3

Відкрий **`/ecosystem` за адресою вебпанелі R3**. Є список до трьох BLE-приладів
із галочками, станом зв’язку, дозволу, часу та поточної сесії.
**Власний STM32-записувач R3 поки не входить у цей список керування.
Адаптер CAN ще не реалізований.**

1. Познач потрібні прилади. START доступний, лише коли всі вибрані свіжі,
   підтверджені, готові, дозволяють керування і мають RTC, звірений із поточним
   R3. Якщо хтось не готовий, команда не ставиться в чергу.
2. Натисни START і дочекайся **«запис триває» для кожного**. «У черзі» або
   «прийнято» ще не доводить початку запису. Збій після відправлення може дати
   частковий результат; фізично одночасного запуску не обіцяємо.
3. STOP стосується вибраних актуальних сесій. Можна явно зупинити й локально
   розпочату сесію, якщо є дозвіл. Місцевий STOP також працює під час STARTING.
   Успіх — після дописування буферів, перевірки й закриття файлу.

Втрата зв’язку або відповіді означає **невідомий стан**, а запис продовжується.
Панель не повторює START після перезавантаження сторінки чи відновлення BLE
і сама не зупиняє прилади, які встигли почати запис. Спочатку перевіряємо їхній
фактичний стан. Запізнілий STOP не має права зачіпати нову сесію.
Повтор пакета з тим самим ідентифікатором обробляється як повтор; нове
натискання кнопки — новий запит із повторною перевіркою стану.

Видалення приладу в R3 скасовує довіру, **але не зупиняє запис**. Для чистого
повторного додавання видали також локальну прив’язку R1.

## Що збережеться у файлах

Нові місцеві й віддалені записи мають [CSV schema 2](../FILE_FORMAT_V2.md):
ідентичність приладу/запуску/сесії, групу та координатора для віддаленого
старту, а також дані останнього звіряння RTC, якщо воно було. Локальний запис
може мати час від R3 без входження до групи. Кожна частина після ротації
повторює весь цей опис. Читання старих CSV v1 збережено.

Похибка часу позначається `null`, тобто невідома, а не нульова. Дані групи
й джерела часу допомагають знайти пов’язані записи, але ще не дають точного
спільного графіка. Модель поправки/дрейфу, часові події й перевірка CAN —
наступні окремі роботи. Апаратні результати — у
[звіті v0.24](../ECOSYSTEM_ACCEPTANCE_2026-09-09.md) та
[журналі міграції](../R1_MIGRATION.md).

У тесті SAVE 0 дозволив звіряння RTC та заборонив віддалений Start. Після
SAVE 1 реальні кнопки R3 запустили й закрили запис на 50 Гц: 549 рядків,
обидва читачі підтвердили цілісність без пропусків. Перезапуск R3 під час
місцевого запису не змінив запуск R1 чи його файл: 722 рядки перевірено;
після відновлення зв’язку RTC чекав закриття файлу. R1 також залишився
автономно готовим після перезапуску з вимкненим BLE R3, а після його ввімкнення
сам підтвердив зв’язок і звірив час. Налаштування повернуто до збереженого
покоління 3 без запису EEPROM.

Окремий результат 300 Гц дивись у звіті: лічильники запису не замінюють
перевірки завантаженого файлу. Три фізичні прилади, недостовірний RTC R3,
раптове повне зникнення живлення й точність вирівнювання ще не перевірено.
