druzvv-hash/r1-s3-logger/docs/uk/ECOSYSTEM_TIME_SYNC.md

# Спільний час R1-S3, R3 та CAN

Рішення від 09.09.2026, реалізація PANEL v0.24.
[Основний технічний документ](../ECOSYSTEM_TIME_SYNC.md) ·
[Прив’язка й керування](ECOSYSTEM_CONTROL.md).
Тести на ПК та [обмежений тест двох плат](../ECOSYSTEM_ACCEPTANCE_2026-09-09.md)
пройдено; це підтверджує дозволи, грубе звіряння RTC, керування й відновлення
після перезапусків, але не точність вирівнювання відліків.

Об’єднуємо прилади, щоб бачити один процес із різних сторін: подію CAN,
струм і просадку напруги R1-S3, швидку реакцію датчиків R3. Кожен записує
свої дані на своїй частоті. Для автономного запису не потрібен постійно
відкритий браузер чи передавання всіх відліків через Bluetooth.

## Що вже закладено в коді

**R3 з RTC RV3028 — головне джерело часу й BLE-сервер. R1-S3 — BLE-клієнт.**
Наявний UART-маяк R3 до STM32 збережено. S1 додав BLE-маяк із захищеним
джерелом, ідентифікатором запуску, ревізією часу та діагностикою пропусків.
[Короткий фізичний тест S1](BLE_ACCEPTANCE_2026-09-09.md) стосується саме
цієї попередньої версії.

PANEL v0.24 додає збережену довіру й автоматичне підключення після запуску,
грубу корекцію RTC у спокої, дозвіл віддаленого керування та START/STOP
вибраних приладів через `/ecosystem` на R3. Після першого захищеного
підключення потрібно явно зберегти прив’язку: лише час або час із керуванням.
Підключення саме по собі не запускає запис.

DS3231 лишається автономним календарем. Корекція від R3 проходить через
власника I²C, зі свіжою відповіддю та перевіркою джерела. Вона чекає, якщо
йде запуск, запис чи закриття файлу; після цього запитується новий час.
Недостовірний час не переноситься. Виміри й енергія завжди використовують
місцевий монотонний час ESP; старі відліки не пересуваються.

[CSV v2](../FILE_FORMAT_V2.md) повторює в кожній частині запису дані приладу,
запуску, сесії, групи й координатора, а також докази останнього звіряння RTC.
Вони фіксуються на старті сесії. Відомий календар може мати невідому похибку
`null`. Старі CSV v1 і їхні правила читання збережено.

## Чого це ще не доводить

**«RTC звірено» ще не означає точного збігу відліків.** R3 читає цілі секунди
програмним опитуванням, без захоплення фізичного фронту RTC. Перевірки віку
відповіді й затримки не вимірюють абсолютну точність чи асиметрію BLE.
Маяк усе ще показує `synchronized=false`, а похибка невідома.

Поточний CSV v2 містить статичне походження часу й групи. У ньому ще немає
моделі поправки/дрейфу, потоку вихідних часових подій чи інтервалів точності
для вирівнювання записів. Після втрати зв’язку запис триває, але нової заяви
про точність немає. Спільний START також не гарантує одночасного відліку.

BLE та вебпанель лишаються на ядрі 0, виміри й окрема задача SD — на ядрі 1.
FIFO у PSRAM та блоковий запис збережено. Власний STM32-записувач R3 поки
не входить у групову панель; адаптер CAN ще не реалізовано.

## Наступні перевірки

1. Розширити пройдені перевірки дозволів, пізнього зв’язку, відкладеної RTC-корекції,
   Start/Stop і перезапусків. Недостовірний RTC R3 та раптове повне зникнення
   живлення ще не тестували фізично; довготривалу роботу й точність вимірів
   перевіряємо окремо. Межі поточного приймання наведено у звіті вище.
2. S2: виміряти затримку, поправку й дрейф за спільною фізичною подією;
   перевірити відповідність часу Control Center до DRDY STM32 та часових міток CAN.
3. S3: додати узгоджені версійовані часові події й відображення похибки у вювері.
   Не називати статичні дані CSV v2 вже готовою точною синхронізацією.
4. S4: три прилади, Wi-Fi, обриви BLE, перезапуски та тривалі записи.

Великий розкид струму на 300 Гц зі старого тесту й розширена радіоперевірка
залишаються відкритими. Якщо похибка двох подій перекривається, їх порядок
не можна впевнено визначити. Старі файли без прив’язки не стануть точними автоматично.
