druzvv-hash/r1-s3-logger/docs/uk/R1_S3_PLAN.md

# План розвитку R1-S3

Версія плану 1.11, 09.09.2026. [Повний технічний план англійською](../R1_S3_PLAN.md) — основний документ для реалізації. [Журнал міграції](../R1_MIGRATION.md) — фактично виконані роботи й результати. Наявність пункту в плані не означає, що його вже реалізовано.

P4a: [панель тестів USB/Wi-Fi](TEST_PANEL.md) реалізована. Вебобслуговування — ядро 0,
виміри та задача SD — ядро 1 із різними пріоритетами. OLED передається частинами,
виміри працюють на 10/50/100 Гц. [Запис сесій на SD](RECORDING.md) підключений
через PSRAM FIFO. P6a: [окрема вкладка Wi-Fi](WIFI.md), запис із закритим браузером
і завантаження файлів через реальний радіозв’язок перевірені на ПК. Перевірка
безпосередньо на Android ще відкрита.
Місцеві меню, тривалі та аварійні апаратні перевірки ще попереду.

## Доповнення 1.10 — спільний час, 09.09.2026

[Синхронізація R1-S3, R3 і CAN](ECOSYSTEM_TIME_SYNC.md) входить до архітектури.
R3 — BLE-сервер і джерело спільного часу, R1-S3 — клієнт. S0 додав розбір
наявного UART-маяка, S1 — BLE на обох приладах. Короткий тест зв’язку й
записів пройдено; розширене приймання, оцінка похибки й динамічні часові події
ще попереду. v0.24 додає статичне походження RTC/групи в CSV v2.
Виміри та енергія лишаються на власному монотонному часі ESP,
втрата BT не зупиняє запис.

## Доповнення 1.11 — головна панель R3, 09.09.2026

**R3 задає час для екосистеми та керує записом на вибраних приладах.**
Після одноразової прив’язки прилад при ввімкненні сам підключається до свого
R3 і звіряє RTC. Без зв’язку використовує власний годинник. Якщо вже йде
запис, корекція RTC чекає закриття файлу; тоді береться свіжий час R3.
Автоматичне підключення не запускає запис.

У R3 буде список приладів із вибором галочками та груповими START/STOP.
Результат видно для кожного: прийняв команду, почав запис, закрив файл або
помилка. Запізніла команда не має зупиняти нову сесію. Втрата BLE не зупиняє
автономний запис і не означає успішний STOP.

[Умови роботи та перевірки](ECOSYSTEM_CONTROL.md). Порядок: **E1 — збережена
прив’язка й підключення після ввімкнення; E2 — звіряння RTC; E3 — команди;
E4 — панель R3; E5 — дані групи й часу у версійованих файлах**. Точність
зіставлення відліків вимірюємо окремо на S2. Оновлення PANEL v0.24 реалізує
E1–E4 та статичні дані походження групи/RTC у CSV v2; тести на ПК пройдено,
[обмежений тест двох плат пройдено](../ECOSYSTEM_ACCEPTANCE_2026-09-09.md),
розширені апаратні перевірки відкриті. Це не точна модель часу S2/S3. Власний
STM32-записувач R3 та CAN поки не входять у групове керування.

## Що будуємо

Самостійний реєстратор напруги, струму, потужності, енергії та заряду на ESP32-S3 + INA228. Зручність R1 зберігаємо, але усуваємо втрату даних, неоднозначні формати, приховані помилки та залежність записів від налаштувань конкретного приладу.

Поточний шунт — 60 мВ / 400 А, тобто 150 мкОм; R015 на модулі видалений. OLED SH1106G, RTC DS3231 у UTC, EEPROM 24C32 і SD вже перевірені на базовому рівні. Поточна прошивка PANEL v0.24 підтримує запис і пряме керування через Wi-Fi. Короткі записи на 10/50/100 Гц перевірені; точність у всьому діапазоні, ALERT, тривала робота та відновлення після зникнення живлення ще не підтверджені.

## Що беремо з попередніх версій

| Джерело | Що використовуємо |
|---|---|
| R1 | Просте START/STOP, покази, окремі додатні/від’ємні енергії, буфер SD, зрозумілий інтерфейс |
| R3 | Збереження сирих даних, версії й контроль цілісності, розділення запису та інтерфейсу, перевірка застосованих налаштувань |
| Вювер Plotly R5 | Маркери, статистика інтервалів, аналіз подій; парсер перепрацьовуємо |
| Вювери LYLI/uPlot | Читання блоками та огляд великих файлів зі збереженням мінімумів/максимумів |

Не переносимо архітектуру STM32/ADS і швидкості R3 в INA228. Не переносимо старі коефіцієнти R1. При помилці датчика не записуємо вигаданий нуль, а при помилці SD не викидаємо буфер мовчки.

## Налаштування та EEPROM

Одна описана схема параметрів: назва, одиниці, значення за замовчуванням, межі, версія, правила зміни й збереження. Групи:

- шунт, полярність і схема підключення;
- нуль і коефіцієнт струму, нуль і коефіцієнт напруги, дата та метод калібрування;
- частота свіжих вимірювань, час перетворення, усереднення і діапазон INA228;
- параметри запису, буфера, збереження й поділу файлів;
- частота оновлення OLED/вебу та фільтрація лише показу;
- часовий пояс відображення; сам RTC зберігає UTC.

Формули визначаємо явно:

```text
I = полярність × (Uшунта_мкВ − нуль_мкВ) / Rшунта_мкОм × коефіцієнт_I
U = (VBUS − нуль_U) × коефіцієнт_U
P = U × I
```

Початкові коефіцієнти 1, поправки нуля 0. Не маскуємо розкид примусовим обнуленням. Температура INA228 не замінює температуру зовнішнього шунта. Калібрування вводимо після вимірювання стабільного нуля й кількох контрольних точок, а не за одним показом ЛБЖ.

EEPROM: дві копії по 1536 байтів, 1024 байти резерву. Кожна має версію, довжину, номер збереження, CRC і завершальний запис. Спочатку записуємо й перевіряємо неактивну копію, тільки потім визнаємо її чинною. При перерваному записі завантажуємо попередню справну. Невідому версію не перезаписуємо автоматично.

Збереження — явною командою, тільки якщо параметри змінилися. Поточні вимірювання, лічильники й енергію щосекунди в EEPROM не пишемо. Перед впровадженням робимо резервну копію всіх 4096 байтів і прибираємо нинішній тест запису при кожному старті. Додаємо експорт/імпорт налаштувань у JSON.

Розрізняємо чернетку, застосовані та збережені налаштування. Калібрування/частоту/час під час запису не змінюємо: STOP, зміна, нова сесія. У файл потрапляють саме параметри, з якими записували.

## Самодостатній файл

Перший власний формат — **R1S3 CSV v1**. У ньому є:

- версія формату, прилад, прошивка та ідентифікатор сесії;
- шунт, одиниці, полярність, коефіцієнти й формули;
- налаштування АЦП, часові параметри та достовірність UTC;
- сирі відліки й значення у В/А/Вт/Вт·год/А·год;
- реальний відносний час, номер відліку та ознаки якості;
- контрольні суми блоків, пропуски та ознака коректного завершення.

Копіюєш один файл на інший ПК — вювер знає, як його прочитати й перерахувати. EEPROM, прилад, чат або сусідній файл конфігурації не потрібні. Приватні мережеві паролі в лог не потрапляють.

Зберігаємо перші вісім знайомих колонок R1; нові поля мають чіткі імена. Фільтр дисплея не змінює сирі записи. Енергію інтегруємо за фактичним часом, не через пропуски. Файли не перезаписуються через однакову хвилину старту. Перервану сесію вювер відкриває як неповну з явною межею перевірених даних.

CSV спершу дає просту перевірку і сумісність. Якщо виміри продуктивності покажуть потребу у BIN для R1-S3, це буде окрема версія формату з власним читачем, а не прихована зміна існуючих файлів.

## Сумісність вювера — обов’язкова частина

Новий вювер має єдину модель даних і окремі читачі:

1. R1 CSV з вісьмома колонками та коментарями.
2. Старі короткі CSV/Pss_Wh; неоднозначні файли без заголовка — з підтвердженням схеми користувачем.
3. Новий R1S3 CSV v1.
4. Перевірені варіанти LYLI/R2 BIN v2.
5. R3 FILELOG V2 із DATA/TCHK, описом каналів і часовими метаданими.

Спочатку забезпечуємо R1 + R1-S3, потім бінарні сімейства. Не обіцяємо підтримку невідомого варіанта без прикладу файлу і відповідного записувача. Навіть старі описи BIN v2 в одній папці суперечать один одному; їхня контрольна сума також має різні варіанти.

Новий вювер читає старі файли. Старий незмінений вювер не обов’язково прочитає новий файл — для нього передбачаємо окремий сумісний експорт із попередженням про втрату нових метаданих/сирих каналів.

Потрібні тести на реальних схемах: порядок колонок, коментарі, відсутні значення, часові збої, старий місцевий час, пошкоджені/обірвані записи. Невідомі значення не перетворюємо в нуль. Стрибки часу розділяємо на сегменти. Графік великих файлів зберігає короткі піки; статистику рахуємо по повних даних. Вювер працює офлайн із локальними бібліотеками.

## Послідовність роботи

| Етап | Що робимо | Коли завершено |
|---|---|---|
| P0 | Фіксуємо робочий HWTEST, схему й резерв EEPROM; відділяємо сервісні тести | Є відтворювана база, звичайний старт не змінює EEPROM і не створює тестові файли |
| P1 | Опис параметрів, EEPROM, формату файлу і матриці сумісності; еталонні файли | Формули, байти, версії, контрольні суми й часові правила однозначні |
| P2 | Ядро вювера та читачі R1/R1-S3 | Тестові файли дають правильні канали/час; неоднозначності й пошкодження видимі |
| P3 | Налаштування та надійне EEPROM-збереження | Пройдені тести пошкодженої копії, перерваного запису, імпорту та старої версії |
| P4 | P4a — локальне й вебкерування, розподіл задач; P4b — постійне вимірювання, реальна частота, калібрування, черга | Частота й пропуски виміряні під навантаженням UI, контрольні точки перевірені |
| P5 | Запис сесій і самодостатній CSV | Файл відкривається вювером, STOP/SD FULL/обрив живлення обробляються явно |
| P6 | Завершення локального/вебінтерфейсу, мережевих налаштувань, live і доступу до файлів | Стан запису зрозумілий, команди узгоджені, робота без Wi-Fi і після закриття браузера перевірена |
| P7 | Тривалі та аварійні тести | Годинний базовий запис, перевірка найвищої дозволеної частоти, відновлення й енергії |
| P8 | Читачі LYLI/R2 і R3, розширені модулі аналізу | Кожен заявлений формат перевірений за записувачем і файлами; опублікована матриця підтримки |

Початкова ціль — 50 свіжих вимірювань/с; кандидати 10/50/100 Гц дозволяємо лише після перевірки часу перетворення, усереднення і навантаження шини. R1-S3 не стає швидшим датчиком лише через швидший цикл ESP32.

Реліз R1-S3 v1 — після P0–P7. Загальну сумісність із бінарними сімействами не вважаємо завершеною до P8. Кожен етап закриваємо результатами, записом у журналі та комітом. Зміни порядку або формату документуємо окремо. **Рішення 08.09.2026: графіки й маркери P2.1a та налаштування P3 готові з описаними межами перевірки. Решту вювера відкладаємо до реальних файлів логера. Далі P4a — керування та задачі, P4b — вимірювання, P5 — запис файлів; потім повертаємося до аналізу й плагінів R5.** [Матриця перенесення](../R5_FEATURE_MIGRATION.md). [Вювер](P2_VIEWER.md). [Результати](P0_P1_RESULTS.md). Стан налаштувань і перевірок EEPROM — у [P3_SETTINGS.md](P3_SETTINGS.md); виробничий запис залишається P5.

## Керування та ядра — уточнення 08.09.2026

Сервісні команди P3 не замінюють користувацький UI. P4a тепер включає вебпанель приладу в стилі пізнього R1/Fnirsi та автономне керування кнопками/енкодером через меню OLED. Власник підтвердив запис на microSD. Точний набір органів керування та GPIO ще уточнюються. Далі P4b — вимірювання, P5 — підключення START/STOP і записів. Вювер файлів поки відкладаємо.

На OLED передбачені великі U/I, сторінки P/енергії/заряду, стан запису та меню сесії, вимірювання, калібрування, екрана, часу й діагностики. Змінюємо чернетку, окремо застосовуємо й зберігаємо. Локальні кнопки, веб і сервісні команди працюють з одним станом; застаріла чернетка не може затерти нові налаштування. START/STOP і налаштування мають працювати без телефона та Wi-Fi.

Ціль: ядро 0 — кнопки/енкодер, меню, веб/UI й підготовка кадрів OLED; ядро 1 — вимірювання та окрема задача запису нижчого пріоритету. Між вимірами й записом — обмежена черга; до UI — копії стану. OLED/INA228 ділять I2C, тому передача дисплея має бути короткими частинами, а не довгим блокуванням шини. Поділ ядер не є гарантією частоти без виміряних затримок. [Повний опис](../DEVICE_UI_AND_TASKS.md).

Уточнення 1.6: вибрано Bourns PEC11R-4220F-S0024, але він ще не встановлений. Заглушка без GPIO та модулі PSRAM FIFO/блокового буфера реалізовані й перевірені на ПК. Початково 64 КіБ PSRAM під 2048 числових відліків, окремо 8 КіБ внутрішньої RAM під блок SD. Це основа, ще не запущений записувач. [Деталі й джерела](BUFFERING_AND_ENCODER.md).
