druzvv-hash/r1-s3-logger/docs/uk/BLE_ACCEPTANCE_2026-09-09.md

# Перевірка BLE R3 ↔ R1-S3 — 2026-09-09

**Короткий тест зв’язку, записів і цілісності файлів пройдено. Розширені
радіотести ще попереду; великий розкид струму на 300 Гц потребує перевірки.**
[Повний звіт англійською](../BLE_ACCEPTANCE_2026-09-09.md) ·
[Як керувати BLE](BLE_LINK.md).

На R1-S3 працювала PANEL v0.23, чиста збірка `f5508af`. R3 — код `0e4925e`
разом зі збереженими попередніми локальними змінами; прошивку STM32 не змінювали.

## Що перевірено

- Пошук на фінальній збірці знайшов R3, після вибору встановився свіжий
  підтверджений зв’язок. Автоматичного вибору чужого приладу немає.
- Правильний PIN: захищене підтверджене з’єднання, MTU 128, маяки надходять.
- Неправильний PIN: R3 відхилив підключення.
- Під час запису 300 Гц вимкнули й увімкнули BLE на R3. R1 автоматично
  перепідключився та почав новий сегмент маяків; запис на SD продовжився.
- Перезапусків R1 у збережених знімках не було. Пропусків вимірів, некоректних
  відліків, помилок I2C і переповнень FIFO — нуль.

Старий UART-маяк R3 також продовжив працювати: R3 повідомив 1 413 відправлень
без помилок, RTC валідний. За його даними CM4 прийняв 1 411 маяків без помилок,
стан `fresh`. Це показники, повідомлені R3, а не окремий тест навантаження STM32.

| Частота | Тривалість за логером | Відліків | Прийнято маяків |
|---:|---:|---:|---:|
| 50 Гц | 21,305 с | 1 053 | 22 |
| 150 Гц | 22,792 с | 3 367 | 24 |
| 300 Гц | 22,635 с | 6 681 | 16 |

Тривалість враховує межі відкриття/закриття сесії, тому її не слід використовувати
для оцінки частоти як «відліки / секунди». У 300 Гц входить навмисний розрив BLE.
Нуль пропущених маяків усередині сегментів не означає доставлення маяків за час
відключення.

Справжня панель працювала паралельно 100,8 секунди: без помилок JavaScript і
втрати зв’язку з UI, мобільна ширина 390 пікселів умістилася. Панель була
**через USB-сервер**. Wi-Fi AP логера був увімкнений, але підключених Wi-Fi
клієнтів не було — роботу панелі телефоном через радіоканал цим не перевірено.

Після тестів повернуто 50 Гц і SAVED, покоління EEPROM 3. Збереження налаштувань
чи встановлення часу не виконувались.

## Файли перевірено

Тестовий скрипт спочатку запитав стару назву `.part`, хоча логер уже завершив
запис і повідомив правильну `.csv` у стані READY. Скрипт виправили й продовжили
перевірку за остаточними шляхами. Це була помилка вибору шляху у тесті.

Усі три CSV завантажено: **11 101 відлік, 2 423 076 байтів**. Обидва читачі
підтвердили цілісність, без пропусків, некоректних рядків чи обірваного хвоста.
За часовими мітками файлів фактичні частоти — 50,000038; 150,014781;
300,029356 Гц. Після завантаження R1 лишався READY, 50 Гц, SAVED/покоління 3,
із підтвердженим BLE-зв’язком і свіжими маяками.

## Якість вимірів на 300 Гц ще не підтверджена

Попри цілі CSV, при близькій до нуля записаній напрузі розкид струму на 300 Гц
значно більший: стандартне відхилення **0,814 А**, діапазон **−1,702…2,481 А**.
На 50 і 150 Гц стандартні відхилення становили 0,011 і 0,018 А.

Це статистика записів, а не еталонний тест шуму: умови входу не калібрувались,
профілі ADC відрізняються, а на 300 Гц був розрив BLE. Причину ще треба
локалізувати. **Успішний транспорт і запис 300 Гц не означають підтвердженої
якості вимірювання на цій частоті.**

Додатково порівняли той самий профіль 300 Гц: BLE увімкнений → вимкнений
на обох платах → знову увімкнений. У кожній фазі брали дані LIVE протягом
10 секунд після 2 секунд очікування. Це вибірка з попереднього перегляду,
а не суцільний запис SD.

| BLE | Відліків LIVE | Середній струм | Стандартне відхилення |
|---|---:|---:|---:|
| Зв’язок до вимкнення | 912 | 0,547 А | 0,936 А |
| Вимкнено на обох платах | 864 | 0,509 А | 0,919 А |
| Зв’язок відновлено | 912 | 0,544 А | 0,908 А |

Великий розкид залишився без BLE. Підстав приписувати його саме BLE цей тест
не дав; повну відсутність впливу радіо він також не доводить. Окремо перевіримо
вхід, землю й режими ADC. Після порівняння повернуто початкові 50 Гц і свіжий
підтверджений зв’язок із R3.

## Що це поки не доводить

Це коротка перевірка зв’язку, не тривалий стрес-тест і не калібрування. Ще не
перевірені поганий радіосигнал, кілька BLE-клієнтів, перезапуски плат, зміна UTC
R3, повне навантаження STM32/CAN і точність взаємного часу.

R1 чесно показує: **маяк отримано, точність синхронізації ще не визначена**.
RTC, EEPROM та CSV v1 не змінювали; записані файли ще не містять доказів
синхронізації. Наступний етап — модель часу з похибкою і її збереження у файлах.
