druzvv-hash/r1-s3-logger/docs/uk/SD_FILES.md

# Файли з картки через панель

1. Відкрий панель логера та вкладку **Файли SD**.
2. Список відкриється автоматично. Прокручуй його, шукай за назвою чи датою,
   сортуй за часом, назвою або розміром. Кнопка **Записи** відкриває папку записів.
3. Вибери файл і натисни **Завантажити**, скористайся стрілкою біля нього
   або двічі клацни назву.

Панель сама дочитує всі сторінки папки. Поки це триває, вона показує, що список
неповний; пошук охоплює вже прочитані файли. **Зупинити** перериває читання списку.
Після завершення пошук працює по всій папці. Для великих списків є окрема область
прокрутки з нерухомими заголовками; на телефоні її можна прокручувати також убік.

Файл збережеться через стандартні завантаження браузера. Там видно прогрес,
можна скасувати завантаження і перевірити, чи воно завершилося. Файл на microSD
залишається. Для папок є кнопки **Відкрити** та **На рівень вище**.

Через USB комп’ютер залишається у своїй мережі. Великі файли краще передавати
через Wi-Fi логера. Одночасно читається один файл або список папки; якщо бачиш
повідомлення про зайняту картку, дочекайся завершення передачі й онови список.
Після тривалої паузи також може знадобитися оновлення списку.

Я можу завантажувати файли через цю саму панель для перевірки їхнього вмісту.
[Запис нових вимірювальних сесій](RECORDING.md) доступний у v0.18. Завантажуй
файли після завершення запису кнопкою Stop.
