druzvv-hash/r1-s3-logger/docs/uk/BUFFERING_AND_ENCODER.md

# Енкодер та буфери

Вибрано **Bourns PEC11R-4220F-S0024**: 24 фіксації, 24 імпульси за оберт, натискання, металевий D-вал 6 мм завдовжки 20 мм. Потрібна ручка під D-вал 6 мм. [Сторінка для замовлення](https://www.tme.eu/en/details/pec11r-4220f-s0024/incremental-type-encoders/bourns/). [Креслення виробника](https://www.bourns.com/docs/product-datasheets/pec11r.pdf). Розміри перевіряємо під корпус; GPIO ще не призначені.

Поки енкодера немає, в коді є заглушка без доступу до GPIO. Майбутнє керування: поворот — вибір/зміна, натискання — підтвердження, довге натискання — назад. Меню має також видимий пункт «Назад». Окрема кнопка REC/STOP можлива, але не обов'язкова.

Для запису беремо числовий FIFO у **PSRAM**, а текст CSV формуватиме записувач. Поточний бюджет 64 КіБ дає 2048 відліків по 32 байти: 40,96 с при 50 Гц, якщо початково черга порожня й записувач зупинився. Це розрахунок місткості, не перевірена допустима затримка SD. Параметр дозволяє збільшення до 1 МіБ; EEPROM автоматично не змінюємо.

У внутрішній RAM — індекси, стеки та блок запису 8 КіБ. FIFO не перезаписує непрочитані дані. Неповний запис на SD фіксує помилку та залишає незаписаний хвіст. Під час нормального запису буфер регулярно спорожнюватиметься; велика PSRAM не замінює синхронізацію файлу й не зберігає дані після втрати живлення.

Від R1 взяли ідею накопичення CSV; від січневого S3 — PSRAM-кільце й блоковий вихід; від R3 — перевірку кількості записаних байтів, синхронізації та втрат. Наявність FIFO в старому коді не усувала блокування: там вимірювання й SD викликались послідовно в одній задачі. У нас це будуть окремі задачі на ядрі 1, UI — на ядрі 0.

У v0.13 підготовлені й перевірені на ПК буферні модулі та виділення пам'яті при старті. Вони ще не підключені до виробничого вимірювання й запису; файли сесій залишаються етапом P5. [Точні джерела, правила й межі перевірки](../BUFFERING_AND_REUSE.md).
