druzvv-hash/r1-s3-logger/hardware/kicad/R3_PowerBox/reports/R3_power_zone_isolation_annotated.pdf

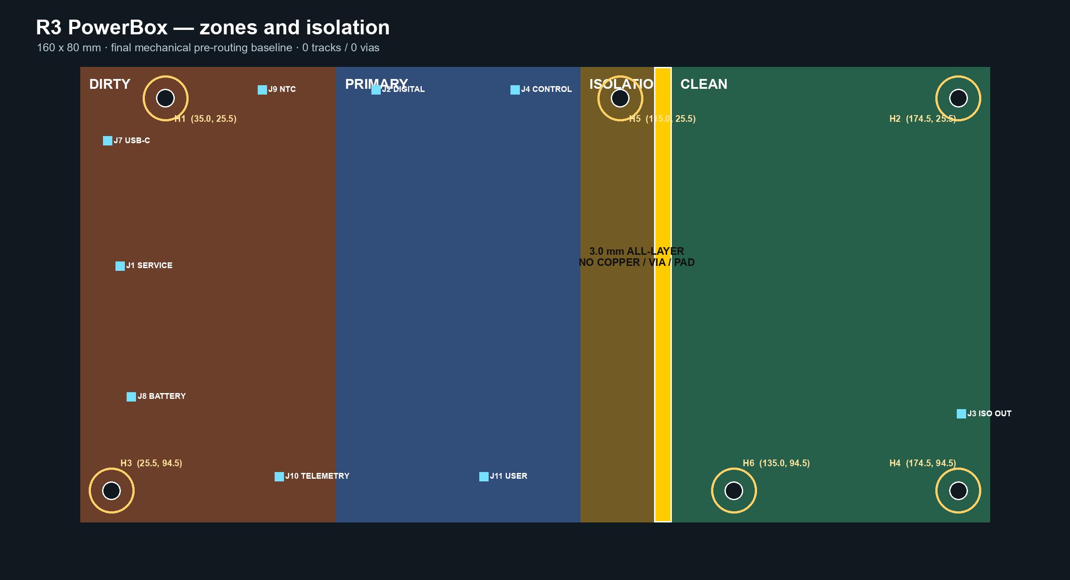
[picture p2: page 1]
