druzvv-hash/r1-s3-logger/hardware/kicad/R3_PowerBox/legacy/README.md

# Legacy migration reference

This folder preserves the earlier KiCad 5 source found in the project material.
It is not the canonical schematic and must not be edited in place. Use the
native KiCad 10 project one directory above for current work.
