druzvv-hash/r1-s3-logger/docs/uk/legacy-r1-analysis.md

# Знайдено стару R1 і в’ювер — 2026-09-07

Фактична папка: `C:\Users\druzv\Desktop\Logger_Analysis`. Варіант `Logger\_Analysis` не існує. Оригінали не змінювалися, нічого зі старих прошивок не заливалося. [Докладний огляд англійською](../legacy-r1-analysis.md).

## Що брати за основу

**Основний кандидат R1 з OLED:** `Projects\bekup\main21_12_3STAB.cpp`, 43 678 bytes, SHA-256 починається з `1d0edfc54f64`.

Він побайтно збігається з `Projects\Temp\main_R1.cpp` та `esp_clamp_logger/src/main.cpp` всередині `Projects\bekup\esp_clamp_logger.7z`. Копії є і в загальному `Projects.7z`. Це суттєвіше за одну назву STAB, але остаточне підтвердження «саме ця остання працювала» ще потребує історичного свідчення або перевірки.

`esp_clamp_logger_R1\src\main.cpp` — старіший варіант від 9 грудня. `esp_clamp_logger_r1_1\main_tft_espi.cpp` має пізнішу дату 1 січня, але це окрема гілка ST7789/TFT, не автоматично краща база для нашого OLED.

У `Projects\esp_clamp_logger\src\main.cpp` тепер лише демонстрація TFT-інтерфейсу. Не переплутати її з робочим кодом із однойменного архіву.

## Відновлений функціонал R1

INA226, окремий ADC напруги GPIO34, SSD1306, DS3231, SD; START/STOP/RESET; частота запитів 1–500 Hz (типово 50), UI/WS 5 Hz; RAM-буфер 8 KiB; потужність і Wh/Whc/Whd; вебпанель, списки/завантаження логів; калібрування в NVS Preferences.

Старий шунт за замовчуванням 50 мкОм і старі коефіцієнти не вважати калібруванням нової INA228. Поточний 24C32 — інший носій конфігурації, ніж старий NVS.

CSV-контракт:

```text
timestamp,ms_from_start,I_A,U_V,P_W,Wh_net,Whc,Whd
```

Його варто зберегти для сумісності, доповнивши явною часовою політикою та метаданими. Стара прошивка могла записувати місцевий час; нова зберігає UTC. Не змішувати їх мовчки.

## Що виправляти при перенесенні

- Ім’я CSV має точність лише до хвилини; повторний START може видалити попередній файл через SD.remove.
- Короткий запис SD не перевіряється, а буфер після запису очищається.
- Помилка читання INA226 повертається як нуль, що може виглядати як нульовий струм.
- 500 читань/с не означають 500 нових перетворень датчика: встановлено усереднення й тривалі перетворення.
- Енергія обчислюється через номінальний dt, хоча SD/HTTP можуть затримувати цикл.
- Старе встановлення часу допускається під час запису; автопідстановка дати збірки після lostPower нам не потрібна.

## В’ювер

**Основний кандидат:** `Viewer\Plugins\viewer_ultimate_Plugins_R5.html` — Plotly, CSV, маркери A/B/C/D, статистика, стартерні події, Live, список логів та плагіни. Окремо є `battery_en.js` і `starter_cycles_advanced.js`. Оцінки EN тут евристичні, це не підтверджений стандартний тест АКБ.

Відтворені проблеми на реальних уривках логів:

1. Plotly читає колонки R1 правильно, але `# rate_hz` і `# interval_us` перетворює на фальшиві нульові точки з неправильними датами. Потрібно пропускати коментарі та перевіряти рядки.
2. `Viewer\Prototype\R5\viewer_ultimate_R5_live_controls_r4.html` — інша, Chart.js-гілка. Вона очікує мілісекунди першою колонкою: сприймає рік 2025 як час, а 132 ms як 132 A. На метаданих падає. Її копія в `Logs\Viewer` ідентична.
3. `viewer_ultimate_R4_3.html` і `viewer_ultimate_R4_2_3_6.html` — однакові байти попри різні назви.
4. В’ювери на uPlot/TypeScript для LYLI BIN v2 належать до ADS/R2, не до CSV R1.

Повний інтерфейс не запускався; перевірено ізольовані CSV-парсери в Node.js. Старі HTML потребують CDN для бібліотек графіків.

## Логи

84 CSV у верхньому `Logs`: кілька поколінь заголовків, є файли без заголовка та з метаданими. У великому `2025_12_03_08_09.csv` виявлено 27 переходів часу назад або без приросту; потрібне розділення сесій, а не припущення про одну суцільну шкалу. Причину переходів не встановлено.

Після INA228 bring-up переносити функції зі STAB поступово, а Plotly-в’ювер відновлювати з виправленим парсером. Старі файли й сирі логи до відкритого репозиторію не копіювалися.
