druzvv-hash/r1-s3-logger/docs/uk/OVERNIGHT_TEST.md

# Нічний тест 8–9 вересня 2026

Запуск о 20:27, заплановане завершення близько 06:27 за місцевим часом.
ЛБЖ вимкнений, дроти підключені. Прошивка 0.22 залишається та сама.

- Спочатку короткий контрольний запис і перевірка завантаженого файла.
- По 20 хвилин запису на 50, 100 та 300 Гц, після кожного — повне завантаження
  через UART та перевірка цілісності й вимірів у файлі.
- Решта десятигодинного вікна — безперервний обмін і вимірювання на 300 Гц.
- Контроль перезапусків, помилок UART, пропусків, FIFO, microSD та пам'яті.

Повна передача великих файлів через UART займає години. Незавершене
завантаження буде позначено окремо й не вважатиметься успішним.

Наприкінці тест повертає початкові 50 Гц без збереження в EEPROM. При збої
зупиняється та зберігає докази; якщо зв'язок втрачено, успішне завершення
запису не можна гарантувати. Автоматичних Reset або перепрошивань немає.

Панель доступна для перегляду. Її керування й файлові операції на час тесту
зайняті перевіркою. ПК потрібно залишити увімкненим; на час тесту сон
тимчасово стримується. Щоб завершити раніше, напиши «зупини нічний тест».

## Результат: тест перервано через UART

Тест завершився 8 вересня о **22:33**, через **2 год 6 хв 19 с**. До кінця
десятигодинного плану не дійшов; повторно його не запускали.

- Запис на **50 Гц**: 60 098 рядків, файл 15,52 МБ повністю завантажений і
  перевірений обома читачами. Пропусків, некоректних рядків і розривів немає.
- Запис на **100 Гц**: логер завершив файл із 120 122 рядками, 30,98 МБ.
  Передача обірвалася після 1,15 МБ. Увесь файл ще не перевірений.
- Етап **300 Гц не розпочався**.
- Windows двічі повідомив **CE_FRAME**; відповідь завантаження містила
  некоректний символ. Це дві фіксації помилки кадру, а не підрахунок
  пошкоджених байтів.
- Логер не перезапускався. За 1356 знімками стану пропусків вимірів, помилок
  I2C і переповнення FIFO немає. Найбільше заповнення FIFO — 14 із 2048 місць.

Автоматичне завершення спочатку не змогло отримати UART через паралельний
запит панелі. Контрольна перевірка відновила зв'язок **без Reset** і о 22:37
підтвердила **READY, 50 Гц, збережений EEPROM покоління 3** та точні початкові
налаштування. Панель працює; нових записів тест не створює.

Отже, UART ще нестабільний навіть із вимкненим ЛБЖ. Конкретну причину ці
дані не визначають. Сирі журнали та неповна копія файла збережені локально.
[Повний технічний звіт](../OVERNIGHT_TEST.md).
