druzvv-hash/r1-s3-logger/docs/uk/bring-up-history.md

# Hardware bring-up

Мета — окремо підтвердити роботу кожного вузла до перенесення старого R1. HWTEST v0.2 реалізує інформацію про пам’ять, I²C scan та SD write/read; інші тести нижче ще потрібно реалізувати.

Оновлення 2026-09-06 за логом власника: v0.1 працює на платі, Flash 33554432 bytes, PSRAM 16774755 bytes. Повторні сканування знаходять 0x3C, 0x40, 0x50, 0x68 без помилок. Тривала стабільність і причина попередніх збоїв не встановлені. v0.2 зібрано; завантаження заблоковане зайнятим/недоступним COM5 (Access denied). Результат SD: NOT RUN.

Спроба 2026-09-06: HWTEST v0.1 успішно зібрано на espressif32 6.12.0 / Arduino 2.0.17. Завантаження через COM5 не почалося: Windows повернула помилку 433 (пристрій не існує). Апаратні результати: NOT RUN.

## 1. Power check

- [ ] Записати фактичні напруги живлення ESP32-S3 та периферії, перевірити спільну землю.
- [ ] Перевірити 3.3 V для логіки й відсутність підтяжок SDA/SCL до 5 V; живлення модулів звірити з їхніми схемами.
- [ ] Переконатися у стабільному старті ESP32-S3 без перезавантажень.

Власник вже повідомив, що напруги в нормі. Для протоколу потрібні числові значення й умови вимірювання.

## 2. I²C scan

- [ ] Запустити сканування на SDA=8, SCL=9, початкова частота 100 kHz.
- [ ] Зафіксувати всі знайдені 7-бітні адреси. Очікуються INA228 `0x40`, OLED `0x3C`, 24C32 `0x50`, RTC `0x68`.
- [ ] Повторити сканування: усі чотири пристрої стабільно відповідають без зависань шини.

Якщо адреса відрізняється, перевірити модель/перемички та оновити документацію. Успішний scan не замінює функціональні тести.

## 3. SD test

У v0.2 тест виконується один раз при старті, SPI 10 MHz. Створюється перший вільний файл `/r1s3_test_0000.txt` … `/r1s3_test_9999.txt`, записується контрольний рядок, файл закривається, карта перемонтовується, розмір і вміст порівнюються побайтно. Успіх: `SD PASS: write, close, remount and exact readback matched.` Файл залишається на карті; автоматичного форматування немає. При кожному RESET створюється наступний файл. Це ще не перевірка збереження після вимкнення живлення. Вставляти картку при вимкненому живленні; закривати Termite/Serial Monitor перед Upload.

- [ ] Ініціалізувати SPI явно: SCK=12, MISO=13, MOSI=11, CS=10. Почати з 10 MHz; при нестабільності знизити частоту.
- [ ] На тестовій картці створити новий файл з унікальним ім'ям, записати відомий рядок і закрити файл.
- [ ] Відкрити файл, прочитати й порівняти вміст; повторити після перезапуску.

Критерій: запис і читання збігаються, дані зберігаються після перезапуску. Наявні файли не перезаписувати.

## 4. OLED

- [ ] Уточнити контролер і роздільність, обрати відповідний драйвер.
- [ ] Вивести назву R1-S3 та тестовий текст; перевірити читабельність і відсутність артефактів.
- [ ] Статуси I²C/SD показувати за реальними результатами тестів.

## 5. EEPROM 24C32

- [ ] Перевірити адресу, стан WP та параметри запису за документацією конкретного чипа.
- [ ] Вибрати тестову ділянку поза даними калібрування; зберегти її початковий вміст.
- [ ] Записати шаблон з урахуванням меж сторінки та часу завершення запису, прочитати й порівняти.
- [ ] Відновити початковий вміст та перевірити відновлення читанням.

Критерій: шаблон і відновлені дані читаються точно, без змін сусідніх адрес.

## 6. RTC

- [ ] Уточнити модель; прочитати дату, час і доступні ознаки втрати живлення/зупинки генератора.
- [ ] Перевірити, що час збільшується між двома читаннями.
- [ ] За наявності резервної батареї перевірити збереження ходу після вимкнення основного живлення.

Не встановлювати час автоматично при кожному старті. Критерій: коректне читання та стабільний хід; валідність часу перевіряється окремо.

## 7. INA228

- [ ] Прочитати Manufacturer ID / Device ID та звірити з документацією INA228.
- [ ] Без значного струму перевірити VBUS, сире значення напруги шунта та температуру чипа.
- [ ] Порівняти VBUS і напругу шунта з мультиметром; записати полярність і нульове зміщення.
- [ ] Уточнити номінал шунта й діапазон вимірювання до обчислення струму та калібрування.
- [ ] Перевірити ALERT на GPIO14 через керовану тестову умову: встановлення та скидання сигналу.

Критерій: ідентифікація збігається, вимірювання узгоджуються з еталоном у заздалегідь обраних допусках, ALERT працює за налаштуванням.

## Протокол результатів

Для кожного кроку записати дату, ревізію/фото стенда, Git commit прошивки, версію PlatformIO/platform, параметри тесту, очікуване й отримане значення, PASS/FAIL і посилання на Serial-лог. Невиконані перевірки позначати NOT RUN.

Після успішних тестів усіх вузлів — починати поетапне перенесення функцій R1: вимірювання, калібрування, CSV/SD-буфер, OLED UI та Web UI.

## SD v0.2: підтверджений запуск 2026-09-06

Прошивку успішно завантажено через COM5; перевірка запису esptool пройдена. Після керованого RESET через RTS: SD 29818 MiB, SPI 10 MHz, файл `/r1s3_test_0001.txt`, запис 39/39 bytes, закриття, перемонтування та побайтне читання — PASS. Після SD ще два I²C scan: усі чотири адреси, 0 помилок. Перевірка після повного вимкнення живлення і тривалий тест не виконані. Лог: [sd-test-v0.2-serial.txt](../sd-test-v0.2-serial.txt).

## OLED v0.3

Попередній драйвер: Adafruit SSD1306 2.5.13, 128x64, адреса 0x3C, I2C 100 kHz на GPIO8/9. На екрані рамка по краях, R1-S3, HWTEST v0.3, число I2C-адрес/помилок, фактичний SD PASS/FAIL та uptime з оновленням раз на секунду. SD-тест зберігає формат рядка v0.2 для сумісності. I2C scan продовжується кожні 10 секунд. Успішна ініціалізація бібліотеки не визначає модель контролера і не підтверджує видиме зображення. Потрібне візуальне підтвердження власника; при порожньому або зміщеному зображенні перевірити модель (зокрема SH1106).

## OLED v0.4

За повідомленням власника, v0.3 завантажено, але SSD1306 дає шум і нечитабельні символи. У v0.4 використано SH1106G 128x64 (Adafruit SH110X 2.1.12), адреса 0x3C, GPIO8/9, 100 kHz. Зображення малюється один раз: рамка по всіх краях, R1-S3, назва драйвера, початкові результати I2C/SD, STATIC TEST v0.4. Періодичний I2C scan у Serial збережено. Візуальна перевірка ще не виконана.

OLED v0.4: власник підтвердив читабельне зображення з драйвером SH1106. Для монтажної орієнтації додано поворот 180 градусів (setRotation(2)); очікує повторного прошивання.

## EEPROM v0.5

24C32, 4096 bytes, I2C 0x50, 16-bit memory address. Перед записом читається повний образ і зберігається в новий файл /eeprom_before_NNNN.bin на SD; файл закривається та перевіряється побайтно. Якщо SD не працює або остання сторінка 0x0FE0–0x0FFF містить дані, відмінні від суцільних FF чи 00, запис пропускається. Тест змінює лише 16 bytes 0x0FE0–0x0FEF, не перетинає межу сторінки, очікує ACK до 25 ms, перевіряє шаблон і відновлює початкові байти навіть після невдалого запису. PASS потребує повного порівняння всіх 4096 bytes з початковим образом. Це вибіркова перевірка запису, не тест усіх комірок. Тест виконується раз на старт; не вимикати живлення до завершення. При RESTORE FAIL зберегти резервну копію й припинити записи. OLED зберігає поворот 180 градусів та показує EEP:PASS/FAIL/SKIP.

Протокол адресації та сторінок: https://ww1.microchip.com/downloads/en/DeviceDoc/doc0336.pdf. Апаратний результат v0.5 ще не підтверджено.

## RTC v0.6

Власник підтвердив SD PASS / EEP PASS на v0.5 та модель RTC DS3231. v0.6 читає регістри 0x00–0x12 з адреси 0x68 без зміни часу, будильників, control/status чи OSF. Перевіряє BCD, календар, 12/24-годинний формат, друкує дату/час, OSF, EOSC та температуру. Кожні 10 секунд порівнює приріст RTC з millis (допуск 1.5 секунди через дискретність читання). На OLED RTC:WAIT, TICK OK, SET TIME (хід є, OSF=1), TICK FAIL, BAD DATE або READ FAIL. TICK OK не підтверджує правильність поточної дати/часу чи батарейне резервування. Century інтерпретується від бази 2000; часовий пояс не призначено. Поворот OLED 180 градусів збережено.

Джерело регістрів: https://www.analog.com/media/en/technical-documentation/data-sheets/ds3231.pdf. Апаратна перевірка v0.6 очікується.

## Поточний режим: UART з ручним входом у завантажувач

За замовчуванням обрано `esp32-s3-uart-manual`, COM5, CDC=0. У ньому `board_upload.before_reset = no_reset` і `board_upload.after_reset = no_reset`. Закрити Serial Monitor/Termite, залишити кабель у UART, затиснути BOOT, натиснути й відпустити RESET, потім відпустити BOOT. Далі запускати Upload саме для esp32-s3-uart-manual. Після успіху натиснути RESET для запуску програми. Профіль вимикає послідовність автоматичного скидання esptool; електричний вплив відкриття порту залежить від USB–UART і схеми плати. USB-профіль збережено для подальшої діагностики, його роботу поки не підтверджено. Конфігурацію та успадкування параметрів перевірено; завантаження цим профілем очікує ручного входу в bootloader.

## 2026-09-07 — час із браузера, HWTEST v0.7

Після перепаювання USB–UART підключена плата пройшла автоматичне прошивання. Причину попередньої несправності остаточно не визначено.

Час узято через Date.now() браузера після прошивання, записано UTC 2026-09-07 05:03:47 (07:03:47 за місцевим часом браузера). DS3231 підтвердив запис, OSF=0/EOSC=0; подальші перевірки ходу PASS. Некоректна команда часу відхилена. При старті час не перезаписується. Для повторення: tools/rtc_sync.py та локальна сторінка http://127.0.0.1:8765. Батарейне збереження ще перевірити.
