druzvv-hash/r1-s3-logger/docs/uk/MEASUREMENT_RATES.md

# Частота вимірів 1–300 Гц

У вкладці **Огляд** є кнопки **1, 5, 10, 25, 50, 100, 150, 200, 250, 300**.
У поле можна вписати будь-яке ціле число з цього діапазону, наприклад **37** або
**137**. Вибери значення, прочитай режим ADC під ним і натисни **Застосувати
частоту** або Enter. Саме введення нічого в логері не змінює.

Починаючи з v0.26, за замовчуванням зберігаються поточні параметри INA228.
Наведені нижче готові режими використовуються лише за явного вибору
**Авто ADC · скинути усереднення**. Власні параметри й узгодження частоти —
у [блоці INA228](INA228_UI.md).

| Частота | Режим |
| --- | --- |
| 1–100 Гц | Звичайний: конверсія 1052 мкс на кожен канал |
| 101–200 Гц | Швидкий: 150 мкс на канал, шум зростає |
| 201–300 Гц | Максимальна швидкість: 50 мкс на канал, більше шуму |

На частотах понад 100 Гц шина переходить на 400 кГц. Усереднення ADC вимкнене
в цих трьох готових режимах. Шунт, коефіцієнти калібрування й діапазон струму
при зміні частоти зберігаються. У розширених налаштуваннях можна задавати власні
параметри ADC; несумісну з частотою тривалість перетворення логер відхилить.

Частоту змінюй між записами: **Stop → дочекатися збереження → нова частота**.
Щоб залишити її після вимкнення живлення, окремо натисни **Зберегти в EEPROM**
в налаштуваннях. Під час наших тестів збереження EEPROM не виконується.

**60 FPS** — плавність малювання графіка. Вона не змінює частоту вимірів.
Для перегляду на високій частоті краще пряме підключення до Wi-Fi логера:
USB через UART 115200 має меншу пропускну здатність. Коли USB не встигає,
графік переходить до свіжої ділянки й позначає пропущені точки як розрив.
Wi-Fi забирає додаткові пакети, якщо накопичилася черга. На SD записуються
всі відліки, незалежно від швидкості браузерного перегляду.

При 1 Гц поріг паузи автоматично збільшується щонайменше до двох секунд,
щоб звичайні інтервали між відліками не переривали підрахунок енергії.
Нові файли читає оновлений вювер; підтримка старих R1/R1-S3 збережена.
Профілі налаштувань із новими частотами мають версію 1.1.

Перевірка 2026-09-08: після заміни USB-кабелю фінальна v0.22 успішно прошилася.
На 300 Гц Wi-Fi-графік пройшов 25 із 25 перевірок актуальності, близько 60 FPS.
Новий файл містить 8376 відліків без пропусків, цілісність підтвердили обидва
читачі. Після тесту повернуто початкові 100 Гц; EEPROM не змінювали. Напис
UNSAVED очікуваний: поточні 100 Гц відрізняються від збереженого профілю.

Точні результати перевірки: [англомовний технічний опис](../MEASUREMENT_RATES.md).
