druzvv-hash/r1-s3-logger/docs/uk/RATE_TESTS_2026-09-08.md

# Частота вимірів: результати 08.09.2026

> Це результати попередньої v0.21. Поточна v0.22 додає діапазон 1–300 Гц та новий розклад роботи UI; див. [частоти вимірювання](../MEASUREMENT_RATES.md).

Поточна звичайна прошивка залишає 10/50/100 Гц. Швидші режими поки дослідні:
ми спочатку перевірили можливості, а рішення про постійні профілі приймемо окремо.

| Варіант | Що перевірено | Обмеження |
|---|---|---|
| 100 Гц, поточний ADC, I²C 100 кГц | 5 хвилин, 30 031 рядок без втрат | Базовий режим; причина першого перезапуску ще невідома |
| 200 Гц, 150 мкс на канал, I²C 400 кГц | 2 хвилини, 23 959 рядків без втрат; окремо прямий Wi-Fi, живий графік близько 60 FPS та OLED | Більший розкид показників; через USB графік іноді відстає |
| 330 Гц, 50 мкс на канал, I²C 400 кГц | 90 секунд, 29 615 рядків без втрат | Панель майже не оновлюється, OLED стоїть; для звичайного користування ще не підходить |
| 350 Гц і вище у швидкому режимі | Вже є пропуски | Цю частоту поточна реалізація не витримує |

У коротких тестах на 100 Гц стандартне відхилення струму зросло з **15,2 мА**
при 1052 мкс на канал до **67,7 мА** при 50 мкс. У довгому тесті 200 Гц / 150 мкс
воно становило **44,5 мА**. Тут разом шум вимірювання, пульсації ЛБЖ/навантаження
та проводки; це не перевірка абсолютної точності й не привід автоматично міняти
калібрування. Середні показники були близько 3,26 В / 3,09 А.

Важливо розрізняти 60 FPS графіка та частоту реальних вимірів. Через UART графік
може плавно рухатися, але відставати від поточного сигналу. У прямому Wi-Fi тесті
200 Гц усі 28 перевірених оновлень були актуальними, без пропусків запису.

Перевірено всі 31 завантажений файл: 30 завершених записів мають правильні
контрольні суми й відкриваються через перевірений адаптер вювера. Дослідні частоти
понад 100 Гц потребують спеціального режиму перевірки; звичайний вювер ще не
вважає їх підтриманим форматом налаштувань. Записи навмисно завищених частот
містять позначені пропуски — цілісний файл не означає, що частота витримана.

Перший самовільний перезапуск залишив `.part` із 13 808 перевіреними рядками
(приблизно 138 секунд). Файл збережений на картці й ПК; завершення запису в ньому
немає. Причину перезапуску не встановлено. У подальшій серії його не відтворено,
але багатогодинну стабільність ще треба перевірити.

Наступний практичний крок — погодити профілі «звичайний / швидкий» із чітким
поясненням шуму, оновити разом формат налаштувань і вювер, а потім провести довші
тести. Для частот близько 330 Гц спочатку треба виправити планування оновлень
стану та OLED; PSRAM-буфер і блоковий запис SD у цих тестах не переповнювалися.

Повні виміри, усі проміжні частоти та межі перевірки — в
[англійському звіті](../RATE_BENCHMARK.md).
