druzvv-hash/r1-s3-logger/docs/uk/TEST_PANEL.md

# Панель тестів R1-S3

На ПК запускай device_ui/start.cmd. Плата підключається через **UART / COM5**.
Termite і Serial Monitor мають бути закриті. Панель тестів працює окремо від в’ювера файлів.

1. **Огляд:** напруга, струм, потужність, температура, графік і стан вузлів.
2. **Налаштування:** змінюй параметри, перевір різницю, натисни **Застосувати**.
   Лише кнопка **Зберегти в EEPROM** збереже їх для наступного запуску.
3. **Діагностика:** сканування I²C, читання SD, два читання EEPROM і вимір INA228.
   Ці тести не створюють файлів і не пишуть тестових шаблонів в EEPROM.
4. **Час із цього пристрою → RTC:** записує UTC з годинника ПК/телефона.
5. Для прошивання: **Діагностика → Звільнити USB для прошивання** або device_ui/stop.cmd.
   Після прошивання знову запусти start.cmd.

Для телефона у вкладці **Wi-Fi** показані назва мережі R1-S3 та пароль.
Там також видно кількість підключених пристроїв і спосіб зв’язку цієї панелі.
Підключись до цієї Wi-Fi мережі, погодься залишитися без інтернету й відкрий
http://192.168.4.1/. Для такого підключення ПК не потрібен.

У **Огляді** вибери **10 / 50 / 100 Гц** і натисни **Застосувати частоту**.
Це змінює реальну частоту INA228. Поточний режим і фактична частота показані вгорі.
Якщо потрібно залишити режим після перезапуску — **Налаштування → Зберегти в EEPROM**.

**60 FPS** — плавність графіка в браузері, незалежна від частоти вимірів.
Можна вибрати 30 FPS і ділянку 10 або 30 секунд. Графік показує справжні відліки;
пауза графіка не зупиняє плату. OLED оновлюється повільніше через спільну I²C-шину.
У **Діагностиці** є кількість пропущених/некоректних відліків і пауз на команди.

Запис сесій на SD працює через FIFO в PSRAM і блоки по 8 KiB.
[Почати запис, зупинити й завантажити файл](RECORDING.md). Енкодер залишається
заглушкою без призначених GPIO.

Калібрування не змінюється автоматично. Значення 150 µΩ відповідає шунту 400 A / 60 mV.
Зміна розміру FIFO застосовується перед наступним записом. Збереження профілю
в EEPROM залишається окремою дією.

[Англійський опис реалізації та перевірок](../P4A_TEST_PANEL.md).

У v0.16 з’явилася вкладка **Файли SD**: список папок і завантаження файлів.
[Інструкція](SD_FILES.md).
