druzvv-hash/r1-s3-logger/docs/uk/LOAD_TEST_2026-09-08.md

# Тест із навантаженням 3 А / 3 В — 8 вересня 2026

Прошивка v0.17 залита. Перевірено 10, 50 і 100 Гц: у контрольних ділянках немає
пропущених або невалідних вимірів, помилок I2C чи розривів послідовності.

На 100 Гц за 30 секунд отримано 3000 послідовних відліків. Середні показники:
**2,9995 А, 2,9988 В, 8,995 Вт**. Це перевірка стабільності при заданому
навантаженні, точність щодо незалежного еталона цього разу не перевіряли.

Далі протягом хвилини на 100 Гц завантажено той самий файл із SD 40 разів.
Усі копії по 4096 байтів збігаються. Вимірювання продовжувалися: 6069 валідних
відліків, без пропусків і помилок I2C. У вибірках цього етапу середні значення
становили **2,9991 А, 3,0005 В, 8,999 Вт**. Вибірки Live не є повним записом
усіх вимірів; такий запис має робити майбутній реєстратор на SD.

Знайдено й виправлено затримку оновлення стану панелі: OLED міг забирати
доступний час перед передачею нового стану. Тепер стан публікується перед
необов'язковим оновленням OLED. Після тестів браузер показав **59,7 FPS**
при частоті вимірів 50 Гц.

Повернуто початкові 50 Гц та всю попередню конфігурацію. Калібрування не
змінювалося, збереження в EEPROM не виконувалося, покоління налаштувань — 3.
Прошивання все ще потребувало повторної спроби; стабільність Upload не вважаємо
остаточно підтвердженою.

Наступний крок за планом — запуск і зупинка запису через UI, FIFO в PSRAM,
запис блоками на microSD та перевірка отриманого файлу у вювері.

[Докладні результати й межі перевірки](../LOAD_TEST_2026-09-08.md).
