druzvv-hash/r1-s3-logger/firmware/include/recording_format.h

#pragma once
#include "recording_buffer.h"
#include "settings_core.h"
#include <string>

namespace recording {
// Portable SHA-256 for file integrity; not authentication.
class Sha256 {
public:
    Sha256();
    void add(const void* bytes, size_t size);
    std::string hex() const;
private:
    void transform(const uint8_t* block);
    uint32_t h_[8]; uint8_t tail_[64] = {}; uint64_t size_ = 0;
};
std::string jsonQuote(const std::string& text);
std::string configJson(const settings::Config& config);
std::string utcText(uint64_t epochUs);
// Local calendar with explicit offset in a FAT-safe name; preserve unique suffix.
std::string sessionId(uint64_t utcUs, uint32_t randomHi, uint32_t randomLo, int32_t localOffsetMin = 0);
struct SessionInfo {
    settings::Config config;
    uint64_t generation = 0, originUs = 0, utcUs = 0;
    uint32_t revision = 0;
    uint16_t manufacturer = 0, device = 0, adc = 0;
    double measuredHz = 0;
    std::string id, commit, version, description;
    bool dirty = false;
    // Schema 2 adds explicit ecosystem provenance. Schema 1 output stays exact.
    uint8_t schema = 1;
    uint64_t groupStartUtcUs = 0;
    uint64_t controlSessionId = 0, groupId = 0, bootId = 0, coordinatorBoot = 0;
    std::string deviceId, coordinatorId;
    struct ClockCorrection {
        bool applied = false;
        std::string authorityId;
        uint64_t authorityBoot = 0, requestId = 0, receivedLocalUs = 0;
        uint64_t appliedLocalUs = 0, sourceCaptureUs = 0;
        uint32_t revision = 0, unixS = 0, sourceReadAgeMs = 0, roundtripUs = 0;
    } clockCorrection;
};
struct Totals { double whc=0, whd=0, ahc=0, ahd=0; };
struct SyncSink : ByteSink { virtual bool sync() = 0; };
// Sole storage-owner serializer. A failed sink/format operation latches failure;
// callers must retain the .part file and never finalize/retry it as a clean file.
class LogWriter {
public:
    LogWriter(BlockBuffer& block, SyncSink& sink) : block_(block), sink_(sink) {}
    void beginSession(const SessionInfo& info);
    bool beginPart(uint32_t part, const std::string& previousSha);
    bool row(const Sample& sample);
    bool checkpointAndSync();
    bool finish(bool rotation, std::string& wholeFileSha);
    bool failed() const { return failed_; }
    uint64_t bytes() const { return offset_; }
    uint64_t rows() const { return rows_; }
    uint64_t sessionRows() const { return sessionRows_; }
    const Totals& totals() const { return totals_; }
private:
    bool append(const std::string& bytes);
    bool checkpoint();
    SessionInfo info_;
    BlockBuffer& block_; SyncSink& sink_; Sha256 hash_;
    uint64_t offset_=0, rows_=0, sessionRows_=0, blockStart_=0, firstSeq_=0, lastSeq_=0;
    uint32_t crc_=0xffffffff, blockRows_=0;
    bool failed_=false, previous_=false, incomplete_=false;
    Sample prior_{}; double priorI_=0, priorP_=0;
    Totals totals_;
};
}
