druzvv-hash/r1-s3-logger/firmware/include/pins.h

#pragma once

namespace pins {
constexpr int I2C_SDA = 8;
constexpr int I2C_SCL = 9;
constexpr int SD_CS = 10;
constexpr int SD_MOSI = 11;
constexpr int SD_SCK = 12;
constexpr int SD_MISO = 13;
constexpr int INA228_ALERT = 14;
}  // namespace pins
