druzvv-hash/r1-s3-logger/tests/test_contracts.py

import copy
import hashlib
import io
import json
from pathlib import Path
import struct
import sys
import tempfile
import unittest

ROOT = Path(__file__).resolve().parents[1]
sys.path.insert(0, str(ROOT/'tools'))
import contracts as c
from make_contract_fixtures import metadata, samples
sys.path.insert(0, str(ROOT/'viewer'))
import core


def ecosystem_metadata(corrected=True, grouped=True):
    meta=metadata();meta['schema']=2
    meta['ecosystem']=dict(version=1,device_id='02:11:22:33:44:55',
        boot_id='123456789abcdef0',recording_id='1020304050607080',
        group_id='1122334455667788' if grouped else None,
        coordinator_id='02:AA:BB:CC:DD:EE' if grouped else None,
        coordinator_boot_id='8877665544332211' if grouped else None,
        rtc_correction=None)
    meta['time'].update(utc_anchor='2026-09-09T00:00:00.000000Z',source='DS3231/R3' if corrected else 'DS3231',uncertainty_us=None)
    if corrected:
        meta['ecosystem']['rtc_correction']=dict(authority_id='02:AA:BB:CC:DD:EE',
            authority_boot_id='8877665544332211',clock_revision=3,request_id='aabbccddeeff0011',
            unix_s=1788911999,received_local_us='9007199254741009',applied_local_us='9007199254991009',
            source_capture_us='18446744073709551615',source_read_age_ms=250,roundtrip_us=100000,
            uncertainty_us=None)
    return meta


def unchecked_empty_file(meta, magic=None, columns=None):
    """Valid byte integrity around deliberately bad semantics, bypassing the writer."""
    metaraw=b'# META '+c.canonical(meta)+b'\n'
    prefix=(magic or c.MAGICS.get(meta.get('schema'),b'# R1S3_LOG schema=99\n'))+metaraw
    prefix+=f'# META_CRC32 {c.crc(metaraw):08X}\n'.encode()
    prefix+=(columns or ','.join(c.COLUMNS)+'\n').encode()
    end=dict(rows=0,sha256=hashlib.sha256(prefix).hexdigest(),clean=True,reason='stop')
    return prefix+b'# END '+c.canonical(end)+b'\n'


class Contracts(unittest.TestCase):
    def test_crc_known_vector(self):
        self.assertEqual(c.crc(b'123456789'), 0xCBF43926)

    def test_config_roundtrip_and_golden(self):
        slot = c.encode_slot(c.defaults(), 1)
        self.assertEqual(len(slot), 1536)
        self.assertEqual(slot, bytes.fromhex((ROOT/'tests/fixtures/config-default-slot.hex').read_text()))
        self.assertEqual(c.decode_slot(slot), (1, c.defaults()))

    def test_config_maximum_strings_fit(self):
        values = c.defaults()
        for f in c.REGISTRY:
            if f['type'] == 'utf8' and f['name'] != 'calibration_utc':
                values[f['name']] = 'x'*f['max_bytes']
        values['calibration_utc'] = '2026-09-07T00:00:00Z'
        self.assertLessEqual(len(c.encode_payload(values)), 1472)
        self.assertEqual(c.decode_slot(c.encode_slot(values, 2))[1], values)
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
